spiricom/Electrobass_embedded/slider/Electrobass_slider/Electrobass_slider.cydsn/codegentemp/CapSense.h

/*******************************************************************************
* File Name: CapSense.h
* Version 2.60
*
* Description:
*  This file provides constants and parameter values for the CapSense CSD
*  component.
*
* Note:
*
********************************************************************************
* Copyright 2013-2016, Cypress Semiconductor Corporation.  All rights reserved.
* You may use this file only in accordance with the license, terms, conditions,
* disclaimers, and limitations in the end user license agreement accompanying
* the software package with which this file was provided.
*******************************************************************************/

#if !defined(CY_CAPSENSE_CSD_CapSense_H)
#define CY_CAPSENSE_CSD_CapSense_H

#include "cytypes.h"
#include "cyfitter.h"
#include "core_cm0_psoc4.h"
#include "CyLib.h"

#include "CapSense_IP.h"
#include "CapSense_SenseClk.h"
#include "CapSense_SampleClk.h"

/* Constants set by Customizer */
#define CapSense_TOTAL_SENSOR_COUNT            (11u)
#define CapSense_TOTAL_SCANSLOT_COUNT          (11u)
#define CapSense_INDEX_TABLE_SIZE              (0u)

/* Define Sensors */
#define CapSense_SENSOR_LINEARSLIDER0_E0__LS    (0u)
#define CapSense_SENSOR_LINEARSLIDER0_E1__LS    (1u)
#define CapSense_SENSOR_LINEARSLIDER0_E2__LS    (2u)
#define CapSense_SENSOR_LINEARSLIDER0_E3__LS    (3u)
#define CapSense_SENSOR_LINEARSLIDER0_E4__LS    (4u)
#define CapSense_SENSOR_LINEARSLIDER0_E5__LS    (5u)
#define CapSense_SENSOR_LINEARSLIDER0_E6__LS    (6u)
#define CapSense_SENSOR_LINEARSLIDER0_E7__LS    (7u)
#define CapSense_SENSOR_LINEARSLIDER0_E8__LS    (8u)
#define CapSense_SENSOR_BUTTON0__BTN    (9u)
#define CapSense_SENSOR_BUTTON1__BTN    (10u)

#define CapSense_TOTAL_SENSOR_MASK (((CapSense_TOTAL_SENSOR_COUNT - 1u) / 8u) + 1u)

/* Interrupt handler */
CY_ISR_PROTO(CapSense_ISR);

/* ISR Number and Priority to work with CyLib functions */
#define CapSense_ISR_NUMBER        (CapSense_ISR__INTC_NUMBER)
#define CapSense_ISR_PRIORITY      (CapSense_ISR__INTC_PRIOR_NUM)

/***************************************
*   Condition compilation parameters
***************************************/

#define CapSense_CONNECT_INACTIVE_SNS       (0u)
#define CapSense_IS_COMPLEX_SCANSLOTS       (0u)
#define CapSense_COMPLEX_SCANSLOTS_NUM      (0u)
#define CapSense_DEDICATED_SENSORS_NUM      (0u)
#define CapSense_PORT_PIN_CONFIG_TBL_ZISE   (11u)

#define CapSense_IDAC_CNT                   (2u)
#define CapSense_IDAC1_POLARITY             (0u)
#define CapSense_IDAC1_RANGE_VALUE          (0u)
#define CapSense_IDAC2_RANGE_VALUE          (0u)

#define CapSense_MULTIPLE_FREQUENCY_SET     (1u)
#define CapSense_FILTER_ENABLE              (0u)
#define CapSense_PRS_OPTIONS                (0u)

#define CapSense_WATER_PROOF                (0u)

#define CapSense_TUNING_METHOD              (0u)
#define CapSense_TUNER_API_GENERATE         (0u)

#define CapSense_CSHL_API_GENERATE          (1u)

#define CapSense_CMOD_PREGARGE_OPTION       (1u)
#define CapSense_CSH_TANK_PREGARGE_OPTION   (1u)
#define CapSense_IS_SHIELD_ENABLE           (0u)
#define CapSense_CSH_TANK_ENABLE            (0u)

#define CapSense_SHIELD_DELAY               (0u)
#define CapSense_AUTOCALIBRATION_ENABLE     (0u)

#define CapSense_IS_OVERSAMPLING_EN         (1u)

#define CapSense_CSD_4B_PWM_MODE            (0u)
#define CapSense_CSD_4B_PWM_COUNT           (0u)

/**************************************
*    Enumerated Types and Parameters
**************************************/

/* Current source definitions */
#define CapSense__IDAC_SOURCE 0
#define CapSense__IDAC_SINK 1

#define CapSense__IDAC_4X 0
#define CapSense__IDAC_8X 1

#define CapSense__PRS_NONE 0
#define CapSense__PRS_8BITS 1
#define CapSense__PRS_12BITS 2
#define CapSense__PRS_AUTO 3

/* Connection of inactive sensors definitions */
#define CapSense__GROUND 0
#define CapSense__HIZ_ANALOG 1
#define CapSense__SHIELD 2

/* Precharge options definitions */
#define CapSense__CAPPRIOBUF 0
#define CapSense__CAPPRVREF 1

/* Method of tuning */
#define CapSense__TUNING_NONE 0
#define CapSense__TUNING_MANUAL 1
#define CapSense__TUNING_AUTO 2

/* Dead band PWM modulator options */
#define CapSense__PWM_OFF 0
#define CapSense__PWM_HIGH 2
#define CapSense__PWM_LOW 3


#define CapSense_DELAY_EXTRACYCLES_NUM          (9u)
#define CapSense_GLITCH_ELIMINATION_TIMEOUT     (0u)
#define CapSense_GLITCH_ELIMINATION_CYCLES_CALC (CapSense_GLITCH_ELIMINATION_TIMEOUT * CYDEV_BCLK__SYSCLK__MHZ)

#if(CapSense_GLITCH_ELIMINATION_CYCLES_CALC >= CapSense_DELAY_EXTRACYCLES_NUM)
    #define CapSense_GLITCH_ELIMINATION_CYCLES (CapSense_GLITCH_ELIMINATION_CYCLES_CALC -\
                                                        CapSense_DELAY_EXTRACYCLES_NUM)
#else
    #define CapSense_GLITCH_ELIMINATION_CYCLES (CapSense_GLITCH_ELIMINATION_CYCLES_CALC)
#endif /* (CapSense_GLITCH_ELIMINATION_CYCLES_CALC >= CapSense_DELAY_EXTRACYCLES_NUM) */

#define CapSense_INITIAL_CLK_DIVIDER            (CYDEV_BCLK__HFCLK__KHZ / CYDEV_BCLK__SYSCLK__KHZ)


/* Structure to save registers before going to sleep */
typedef struct
{
    uint8 enableState;
} CapSense_BACKUP_STRUCT;


/***************************************
*        Function Prototypes
***************************************/
void CapSense_Init(void);
void CapSense_CsdHwBlockInit(void);
void CapSense_Enable(void);
void CapSense_Start(void);
void CapSense_Stop(void);
void CapSense_SaveConfig(void);
void CapSense_Sleep(void);
void CapSense_RestoreConfig(void);
void CapSense_Wakeup(void);
uint32 CapSense_IsBusy(void);
void CapSense_ScanSensor(uint32 sensor);
void CapSense_ScanWidget(uint32 widget);
void CapSense_ScanEnabledWidgets(void);
uint16 CapSense_ReadSensorRaw(uint32 sensor);
void CapSense_WriteSensorRaw(uint32 sensor, uint16 value);
void CapSense_ClearSensors(void);
void CapSense_SetShieldDelay(uint32 delay);
uint32 CapSense_ReadCurrentScanningSensor(void);

uint32 CapSense_GetScanResolution(uint32 widget);
uint32 CapSense_GetSenseClkDivider(uint32 sensor);
uint32 CapSense_GetModulatorClkDivider(uint32 sensor);
uint32 CapSense_GetModulationIDAC(uint32 sensor);
uint32 CapSense_GetCompensationIDAC(uint32 sensor);
uint32 CapSense_GetIDACRange(void);

#if (CapSense_TUNING_METHOD != CapSense__TUNING_NONE)
    void CapSense_SetScanResolution(uint32 widget, uint32 resolution);
    void CapSense_SetSenseClkDivider(uint32 sensor, uint32 senseClk);
    void CapSense_SetModulatorClkDivider(uint32 sensor, uint32 modulatorClk);
    void CapSense_SetModulationIDAC(uint32 sensor, uint32 modIdacValue);
    void CapSense_SetCompensationIDAC(uint32 sensor, uint32 compIdacValue);
    void CapSense_SetIDACRange(uint32 iDacRange);
#endif /* (CapSense_TUNING_METHOD != CapSense__TUNING_NONE) */


void CapSense_SetDriveModeAllPins(uint32 driveMode);
void CapSense_RestoreDriveModeAllPins(void);
void CapSense_SetUnscannedSensorState(uint32 sensor, uint32 sensorState);
void CapSense_NormalizeWidgets(uint32 widgetsNum, uint8 dataPtr[]);

/***************************************
*           API Constants
***************************************/

/* PWM Resolution */
#define CapSense_CNT_MSB_RESOLUTION_8_BITS  (0x00u)
#define CapSense_CNT_MSB_RESOLUTION_9_BITS  (0x01u)
#define CapSense_CNT_MSB_RESOLUTION_10_BITS (0x03u)
#define CapSense_CNT_MSB_RESOLUTION_11_BITS (0x07u)
#define CapSense_CNT_MSB_RESOLUTION_12_BITS (0x0Fu)
#define CapSense_CNT_MSB_RESOLUTION_13_BITS (0x1Fu)
#define CapSense_CNT_MSB_RESOLUTION_14_BITS (0x3Fu)
#define CapSense_CNT_MSB_RESOLUTION_15_BITS (0x7Fu)
#define CapSense_CNT_MSB_RESOLUTION_16_BITS (0xFFu)

#define CapSense_ONE_CYCLE                  (0x00010000Lu)

#define CapSense_WINDOW_APPEND              (0xFFFF0000Lu)
#define CapSense_RESOLUTION_6_BITS          (0x003F0000Lu)
#define CapSense_RESOLUTION_7_BITS          (0x007F0000Lu)
#define CapSense_RESOLUTION_8_BITS          (0x00FF0000Lu)
#define CapSense_RESOLUTION_9_BITS          (0x01FF0000Lu)
#define CapSense_RESOLUTION_10_BITS         (0x03FF0000Lu)
#define CapSense_RESOLUTION_11_BITS         (0x07FF0000Lu)
#define CapSense_RESOLUTION_12_BITS         (0x0FFF0000Lu)
#define CapSense_RESOLUTION_13_BITS         (0x1FFF0000Lu)
#define CapSense_RESOLUTION_14_BITS         (0x3FFF0000Lu)
#define CapSense_RESOLUTION_15_BITS         (0x7FFF0000Lu)
#define CapSense_RESOLUTION_16_BITS         (0xFFFF0000Lu)

#define CapSense_RESOLUTION_OFFSET          (16u)
#define CapSense_MSB_RESOLUTION_OFFSET      (22u)
#define CapSense_RESOLUTIONS_TBL_SIZE       (3u)

/* Software Status Register Bit Masks */
#define CapSense_SW_STS_BUSY                (0x01u)
/* Software Control Register Bit Masks */
#define CapSense_SW_CTRL_SINGLE_SCAN        (0x80u)

/* Software Control Register Bit Masks for scanning one widget */
#define CapSense_SW_CTRL_WIDGET_SCAN        (0x40u)

/* Flag for complex scan slot */
#define CapSense_COMPLEX_SS_FLAG            (0x80u)

/* Flag for scanning is complete */
#define CapSense_NOT_SENSOR                 (0xFFFFFFFFLu)

/* Number of bits for each pin in PC register. */
#define CapSense_PC_PIN_CFG_SIZE            (0x03u)

/* Number of bits for each pin in HSIOM register. */
#define CapSense_HSIOM_PIN_CFG_SIZE         (0x04u)

#define CapSense_CFG_REG_TBL_SIZE           (5u)

/***************************************
*             Registers
***************************************/

#define CapSense_CSD_ID_REG             (*(reg32 *)  CapSense_CSD_FFB__CSD_ID)
#define CapSense_CSD_ID_PTR             ( (reg32 *)  CapSense_CSD_FFB__CSD_ID)

#define CapSense_CSD_CFG_REG            (*(reg32 *)  CapSense_CSD_FFB__CSD_CONFIG)
#define CapSense_CSD_CFG_PTR            ( (reg32 *)  CapSense_CSD_FFB__CSD_CONFIG)

#define CapSense_CSD_IDAC_REG           (*(reg32 *)  CapSense_IDAC1_cy_psoc4_idac__CSD_IDAC)
#define CapSense_CSD_IDAC_PTR           ( (reg32 *)  CapSense_IDAC1_cy_psoc4_idac__CSD_IDAC)

#define CapSense_CSD_CNT_REG            (*(reg32 *) CapSense_CSD_FFB__CSD_COUNTER)
#define CapSense_CSD_CNT_PTR            ( (reg32 *) CapSense_CSD_FFB__CSD_COUNTER)

#define CapSense_CSD_STAT_REG           (*(reg32 *) CapSense_CSD_FFB__CSD_STATUS)
#define CapSense_CSD_STAT_PTR           ( (reg32 *) CapSense_CSD_FFB__CSD_STATUS)

#define CapSense_CSD_INTR_REG           (*(reg32 *) CapSense_CSD_FFB__CSD_INTR)
#define CapSense_CSD_INTR_PTR           ( (reg32 *) CapSense_CSD_FFB__CSD_INTR)

#define CapSense_CSD_INTR_SET_REG       (*(reg32 *) CapSense_CSD_FFB__CSD_INTR_SET)
#define CapSense_CSD_INTR_SET_PTR       ( (reg32 *) CapSense_CSD_FFB__CSD_INTR_SET)

#define CapSense_CSD_4B_PWM_REG         (*(reg32 *) CapSense_CSD_FFB__CSD_PWM)
#define CapSense_CSD_4B_PWM_PTR         ( (reg32 *) CapSense_CSD_FFB__CSD_PWM)

#define CapSense_CSD_TRIM1_REG          (*(reg32 *) CapSense_IDAC1_cy_psoc4_idac__CSD_TRIM1)
#define CapSense_CSD_TRIM1_PTR          ( (reg32 *) CapSense_IDAC1_cy_psoc4_idac__CSD_TRIM1)

#define CapSense_CSD_TRIM2_REG          (*(reg32 *) CapSense_IDAC1_cy_psoc4_idac__CSD_TRIM2)
#define CapSense_CSD_TRIM2_PTR          ( (reg32 *) CapSense_IDAC1_cy_psoc4_idac__CSD_TRIM2)

#if (2u == CapSense_M0S8CSD_BLOCK_CNT)
    #if (CapSense_CSD_FFB__CSD_NUMBER != 1u)
        #define CapSense_SFLASH_CSD_TRIM1_REG   (*(reg8 *) CYREG_SFLASH_CSD_TRIM1_CSD)
        #define CapSense_SFLASH_CSD_TRIM1_PTR   ( (reg8 *) CYREG_SFLASH_CSD_TRIM1_CSD)

        #define CapSense_SFLASH_CSD_TRIM2_REG   (*(reg8 *) CYREG_SFLASH_CSD_TRIM2_CSD)
        #define CapSense_SFLASH_CSD_TRIM2_PTR   ( (reg8 *) CYREG_SFLASH_CSD_TRIM2_CSD)
    #else
        #define CapSense_SFLASH_CSD_TRIM1_REG   (*(reg8 *) CYREG_SFLASH_CSD1_TRIM1_CSD)
        #define CapSense_SFLASH_CSD_TRIM1_PTR   ( (reg8 *) CYREG_SFLASH_CSD1_TRIM1_CSD)

        #define CapSense_SFLASH_CSD_TRIM2_REG   (*(reg8 *) CYREG_SFLASH_CSD1_TRIM2_CSD)
        #define CapSense_SFLASH_CSD_TRIM2_PTR   ( (reg8 *) CYREG_SFLASH_CSD1_TRIM2_CSD)
    #endif /* (CapSense_CSD_FFB__CSD_NUMBER != 1u) */
#else
    #define CapSense_SFLASH_CSD_TRIM1_REG   (*(reg8 *) CYREG_SFLASH_CSD_TRIM1_CSD)
    #define CapSense_SFLASH_CSD_TRIM1_PTR   ( (reg8 *) CYREG_SFLASH_CSD_TRIM1_CSD)

    #define CapSense_SFLASH_CSD_TRIM2_REG   (*(reg8 *) CYREG_SFLASH_CSD_TRIM2_CSD)
    #define CapSense_SFLASH_CSD_TRIM2_PTR   ( (reg8 *) CYREG_SFLASH_CSD_TRIM2_CSD)
#endif /* (2u == CapSense_M0S8CSD_BLOCK_CNT) */

/* Port function select */
#define CapSense_PORT_SEL0_REG          (*(reg32 *) CYREG_HSIOM_PORT_SEL0 )
#define CapSense_PORT_SEL0_PTR          (*(reg32 *) CYREG_HSIOM_PORT_SEL0 )

#define CapSense_PORT_SEL1_REG          (*(reg32 *) CYREG_HSIOM_PORT_SEL1 )
#define CapSense_PORT_SEL1_PTR          (*(reg32 *) CYREG_HSIOM_PORT_SEL1 )

#define CapSense_PORT_SEL2_REG          (*(reg32 *) CYREG_HSIOM_PORT_SEL2 )
#define CapSense_PORT_SEL2_PTR          (*(reg32 *) CYREG_HSIOM_PORT_SEL2 )

#define CapSense_PORT_SEL3_REG          (*(reg32 *) CYREG_HSIOM_PORT_SEL3 )
#define CapSense_PORT_SEL3_PTR          (*(reg32 *) CYREG_HSIOM_PORT_SEL3 )

#define CapSense_PORT_SEL4_REG          (*(reg32 *) CYREG_HSIOM_PORT_SEL4 )
#define CapSense_PORT_SEL4_PTR          (*(reg32 *) CYREG_HSIOM_PORT_SEL4 )


#define CapSense_PORT0_PC_REG          (*(reg32 *) CYREG_PRT0_PC )
#define CapSense_PORT0_PC_PTR          (*(reg32 *) CYREG_PRT0_PC )

#define CapSense_PORT1_PC_REG          (*(reg32 *) CYREG_PRT1_PC )
#define CapSense_PORT1_PC_PTR          (*(reg32 *) CYREG_PRT1_PC )

#define CapSense_PORT2_PC_REG          (*(reg32 *) CYREG_PRT2_PC )
#define CapSense_PORT2_PC_PTR          (*(reg32 *) CYREG_PRT2_PC )

#define CapSense_PORT3_PC_REG          (*(reg32 *) CYREG_PRT3_PC )
#define CapSense_PORT3_PC_PTR          (*(reg32 *) CYREG_PRT3_PC )

#define CapSense_PORT4_PC_REG          (*(reg32 *) CYREG_PRT4_PC )
#define CapSense_PORT4_PC_PTR          (*(reg32 *) CYREG_PRT4_PC )


#define CapSense_PORT0_DR_REG          (*(reg32 *) CYREG_PRT0_DR )
#define CapSense_PORT0_DR_PTR          (*(reg32 *) CYREG_PRT0_DR )

#define CapSense_PORT1_DR_REG          (*(reg32 *) CYREG_PRT1_DR )
#define CapSense_PORT1_DR_PTR          (*(reg32 *) CYREG_PRT1_DR )

#define CapSense_PORT2_DR_REG          (*(reg32 *) CYREG_PRT2_DR )
#define CapSense_PORT2_DR_PTR          (*(reg32 *) CYREG_PRT2_DR )

#define CapSense_PORT3_DR_REG          (*(reg32 *) CYREG_PRT3_DR )
#define CapSense_PORT3_DR_PTR          (*(reg32 *) CYREG_PRT3_DR )

#define CapSense_PORT4_DR_REG          (*(reg32 *) CYREG_PRT4_DR )
#define CapSense_PORT4_DR_PTR          (*(reg32 *) CYREG_PRT4_DR )



#define CapSense_CMOD_CONNECTION_REG        (*(reg32 *) CapSense_Cmod__0__HSIOM)
#define CapSense_CMOD_PORT_PC_REG           (*(reg32 *) CapSense_Cmod__0__PC)
#define CapSense_CMOD_PORT_DR_REG           (*(reg32 *) CapSense_Cmod__0__DR)

#define CapSense_CTANK_CONNECTION_REG       (*(reg32 *) CapSense_Csh_tank__0__HSIOM)
#define CapSense_CTANK_PORT_PC_REG          (*(reg32 *) CapSense_Csh_tank__0__PC)
#define CapSense_CTANK_PORT_DR_REG          (*(reg32 *) CapSense_Csh_tank__0__DR)

/***************************************
*       Register Constants
***************************************/

/* Port configuration defines */
#define CapSense_CSD_HSIOM_MASK                 (0x0000000FLu)

#define CapSense_CSD_SENSE_PORT_MODE            (0x00000004Lu)
#define CapSense_CSD_SHIELD_PORT_MODE           (0x00000005Lu)

#define CapSense_AMUXA_CONNECTION_MODE          (0x00000006Lu)
#define CapSense_AMUXB_CONNECTION_MODE          (0x00000007Lu)

#define CapSense_CSD_PIN_MODE_MASK              (0x00000007Lu)
#define CapSense_CSD_PIN_DRIVE_MASK             (0x00000001Lu)

#define CapSense_CSD_PIN_DM_STRONG              (0x00000006Lu)
#define CapSense_CSD_PIN_DM_HIGH_Z              (0x00000000Lu)

#define CapSense_CSD_CMOD_CONNECTION_MASK   (uint32)(CapSense_Cmod__0__HSIOM_MASK)
#define CapSense_CSD_CMOD_TO_AMUXBUS_A      (uint32)(CapSense_AMUXA_CONNECTION_MODE << CapSense_Cmod__0__HSIOM_SHIFT)
#define CapSense_CSD_CMOD_TO_AMUXBUS_B      (uint32)(CapSense_AMUXB_CONNECTION_MODE << CapSense_Cmod__0__HSIOM_SHIFT)

#if(0u != CapSense_CSH_TANK_ENABLE)
    #define CapSense_CSD_CTANK_CONNECTION_MASK  (uint32)(CapSense_Csh_tank__0__HSIOM_MASK)
    #define CapSense_CSD_CTANK_TO_AMUXBUS_A     (uint32)(CapSense_AMUXA_CONNECTION_MODE << CapSense_Csh_tank__0__HSIOM_SHIFT)
    #define CapSense_CSD_CTANK_TO_AMUXBUS_B     (uint32)(CapSense_AMUXB_CONNECTION_MODE << CapSense_Csh_tank__0__HSIOM_SHIFT)
#endif /* (0u != CapSense_CSH_TANK_ENABLE) */

#define  CapSense_CSD_CMOD_PC_MASK          (uint32)(CapSense_CSD_PIN_MODE_MASK <<\
                                                            ((uint32)CapSense_Cmod__0__SHIFT * CapSense_PC_PIN_CFG_SIZE))
#define  CapSense_CMOD_PC_STRONG_MODE       (uint32)(CapSense_CSD_PIN_DM_STRONG <<\
                                                            ((uint32)CapSense_Cmod__0__SHIFT * CapSense_PC_PIN_CFG_SIZE))
#define  CapSense_CMOD_PC_HIGH_Z_MODE       (uint32)(CapSense_CSD_PIN_DM_HIGH_Z <<\
                                                            ((uint32)CapSense_Cmod__0__SHIFT * CapSense_PC_PIN_CFG_SIZE))

#if(0u != CapSense_CSH_TANK_ENABLE)
    #define  CapSense_CSD_CTANK_PC_MASK         (uint32)(CapSense_CSD_PIN_MODE_MASK <<\
                                                                ((uint32)CapSense_Csh_tank__0__SHIFT * CapSense_PC_PIN_CFG_SIZE))
    #define  CapSense_CTANK_PC_STRONG_MODE      (uint32)(CapSense_CSD_PIN_DM_STRONG <<\
                                                                ((uint32)CapSense_Csh_tank__0__SHIFT * CapSense_PC_PIN_CFG_SIZE))
    #define  CapSense_CTANK_PC_HIGH_Z_MODE      (uint32)(CapSense_CSD_PIN_DM_HIGH_Z <<\
                                                                ((uint32)CapSense_Csh_tank__0__SHIFT * CapSense_PC_PIN_CFG_SIZE))
#endif /* (0u != CapSense_CSH_TANK_ENABLE) */

#define  CapSense_CMOD_DR_VSSIO             (uint32)(CapSense_Cmod__0__MASK)
#define  CapSense_CMOD_DR_VDDIO             (0x00000000Lu)
#define  CapSense_CMOD_DR_MASK              (uint32)(CapSense_Cmod__0__MASK)

#if(0u != CapSense_CSH_TANK_ENABLE)
    #define  CapSense_CTANK_DR_VSSIO            (uint32)(CapSense_Csh_tank__0__MASK)
    #define  CapSense_CTANK_DR_VDDIO            (0x00000000Lu)
    #define  CapSense_CTANK_DR_MASK             (uint32)(CapSense_Csh_tank__0__MASK)
#endif /* (0u != CapSense_CSH_TANK_ENABLE) */

#define  CapSense_CMOD_PIN_NUMBER               (CapSense_Cmod__0__SHIFT)
#define  CapSense_CMOD_PRT_NUMBER               (CapSense_Cmod__0__PORT)

#if(0u != CapSense_CSH_TANK_ENABLE)
    #define  CapSense_CTANK_PIN_NUMBER          (CapSense_Csh_tank__0__SHIFT)
    #define  CapSense_CTANK_PRT_NUMBER          (CapSense_Csh_tank__0__PORT)
#endif /* (0u != CapSense_CSH_TANK_ENABLE) */

/* ID register fields position */
#define CapSense_CSD_ID_ID__POS                 (0x00u)
#define CapSense_CSD_ID_REV__POS                (0x10u)

#define CapSense_CSD_ID_ID                      (0xFFLu << CapSense_CSD_ID_ID__POS)
#define CapSense_CSD_ID_REV                     (0xFFLu << CapSense_CSD_ID_REV__POS)

/* CSD_CONFIG register fields position */
#define CapSense_CSD_CFG_DSI_SAMPLE_EN_POS      (0x00u)
#define CapSense_CSD_CFG_SAMPLE_SYNC_POS        (0x01u)
#define CapSense_CSD_CFG_FILTER_EN_POS          (0x03u)
#define CapSense_CSD_CFG_PRS_CLEAR_POS          (0x05u)
#define CapSense_CSD_CFG_PRS_SELECT_POS         (0x06u)
#define CapSense_CSD_CFG_PRS_12_8_POS           (0x07u)
#define CapSense_CSD_CFG_DSI_SENSE_EN_POS       (0x08u)
#define CapSense_CSD_CFG_SHIELD_DELAY_POS       (0x09u)
#define CapSense_CSD_CFG_SENSE_COMP_BW_POS      (0x0Bu)
#define CapSense_CSD_CFG_SENSE_EN_POS           (0x0Cu)
#define CapSense_CSD_CFG_REFBUF_EN_POS          (0x0Du)
#define CapSense_CSD_CFG_CHARGE_IO_POS          (0x0Eu)
#define CapSense_CSD_CFG_COMP_PIN_POS           (0x0Fu)
#define CapSense_CSD_CFG_POLARITY_POS           (0x10u)
#define CapSense_CSD_CFG_MUTUAL_CAP_POS         (0x12u)
#define CapSense_CSD_CFG_SENSE_COMP_EN_POS      (0x13u)
#define CapSense_CSD_CFG_REFBUF_OUTSEL_POS      (0x15u)
#define CapSense_CSD_CFG_SENSE_INSEL_POS        (0x16u)
#define CapSense_CSD_REFBUF_DRV_POS             (0x17u)
#define CapSense_CSD_CFG_DDFTSEL_POS            (0x1Au)
#define CapSense_CSD_CFG_ADFTEN_POS             (0x1Du)
#define CapSense_CSD_CFG_DDFTCOMP_POS           (0x1Eu)
#define CapSense_CSD_CFG_ENABLE_POS             (0x1Fu)

/* CSD_STATUS register fields position */
#define CapSense_CSD_STAT_CSD_CHARGE_POS        (0x00u)
#define CapSense_CSD_STAT_CSD_SENSE_POS         (0x01u)
#define CapSense_CSD_STAT_COMP_OUT_POS          (0x02u)
#define CapSense_CSD_STAT_SAMPLE_POS            (0x03u)

/* CSD_IDAC control register fields position */
#define CapSense_CSD_IDAC1_MODE_MASK_POS        (0x08u)
#define CapSense_CSD_IDAC1_MODE_FIXED_POS       (0x08u)
#define CapSense_CSD_IDAC1_MODE_VARIABLE_POS    (0x08u)
#define CapSense_CSD_IDAC1_MODE_DSI_POS         (0x08u)
#define CapSense_CSD_IDAC1_RANGE_8X_POS         (0x0Au)
#define CapSense_CSD_IDAC1_DATA_MASK_POS        (0x00u)

#define CapSense_CSD_IDAC2_MODE_MASK_POS        (0x18u)
#define CapSense_CSD_IDAC2_MODE_FIXED_POS       (0x18u)
#define CapSense_CSD_IDAC2_MODE_VARIABLE_POS    (0x18u)
#define CapSense_CSD_IDAC2_MODE_DSI_POS         (0x18u)
#define CapSense_CSD_IDAC2_RANGE_8X_POS         (0x1Au)
#define CapSense_CSD_IDAC2_DATA_MASK_POS        (0x10u)

/* CSD_COUNTER register fields position */
#define CapSense_CSD_CNT_COUNTER_POS            (0x00u)
#define CapSense_CSD_CNT_PERIOD_POS             (0x10u)

/* CSD_CONFIRG register definitions */
#define CapSense_CSD_CFG_DSI_SAMPLE_EN          (0x01Lu << CapSense_CSD_CFG_DSI_SAMPLE_EN_POS)
#define CapSense_CSD_CFG_SAMPLE_SYNC            (0x01Lu << CapSense_CSD_CFG_SAMPLE_SYNC_POS)
#define CapSense_CSD_CFG_FILTER_EN              (0x01Lu << CapSense_CSD_CFG_FILTER_EN_POS)
#define CapSense_CSD_CFG_PRS_CLEAR              (0x01Lu << CapSense_CSD_CFG_PRS_CLEAR_POS)
#define CapSense_CSD_CFG_PRS_SELECT             (0x01Lu << CapSense_CSD_CFG_PRS_SELECT_POS)
#define CapSense_CSD_CFG_PRS_12_8               (0x01Lu << CapSense_CSD_CFG_PRS_12_8_POS)
#define CapSense_CSD_CFG_DSI_SENSE_EN           (0x01Lu << CapSense_CSD_CFG_DSI_SENSE_EN_POS)
#define CapSense_CSD_CFG_SHIELD_DELAY_MASK      (0x03Lu << CapSense_CSD_CFG_SHIELD_DELAY_POS)
#define CapSense_CSD_CFG_SENSE_COMP_BW          (0x01Lu << CapSense_CSD_CFG_SENSE_COMP_BW_POS)
#define CapSense_CSD_CFG_SENSE_EN               (0x01Lu << CapSense_CSD_CFG_SENSE_EN_POS)
#define CapSense_CSD_CFG_REFBUF_EN              (0x01Lu << CapSense_CSD_CFG_REFBUF_EN_POS)
#define CapSense_CSD_CFG_CHARGE_IO              (0x01Lu << CapSense_CSD_CFG_CHARGE_IO_POS)
#define CapSense_CSD_CFG_COMP_PIN_CH2           (0x01Lu << CapSense_CSD_CFG_COMP_PIN_POS)
#define CapSense_CSD_CFG_POLARITY_VDDIO         (0x01Lu << CapSense_CSD_CFG_POLARITY_POS)
#define CapSense_CSD_CFG_MUTUAL_CAP             (0x01Lu << CapSense_CSD_CFG_MUTUAL_CAP_POS)
#define CapSense_CSD_CFG_SENSE_COMP_EN          (0x01Lu << CapSense_CSD_CFG_SENSE_COMP_EN_POS)
#define CapSense_CSD_CFG_REFBUF_OUTSEL          (0x01Lu << CapSense_CSD_CFG_REFBUF_OUTSEL_POS)
#define CapSense_CSD_CFG_SENSE_INSEL            (0x01Lu << CapSense_CSD_CFG_SENSE_INSEL_POS)
#define CapSense_CSD_REFBUF_DRV_MASK            (0x03Lu << CapSense_CSD_REFBUF_DRV_POS)
#define CapSense_CSD_REFBUF_DRV_LOW             (0x01Lu << CapSense_CSD_REFBUF_DRV_POS)
#define CapSense_CSD_REFBUF_DRV_MEDIUM          (0x02Lu << CapSense_CSD_REFBUF_DRV_POS)
#define CapSense_CSD_REFBUF_DRV_HIGH            (0x03Lu << CapSense_CSD_REFBUF_DRV_POS)
#define CapSense_CSD_CFG_DDFTSEL_MASK           (0x07Lu << CapSense_CSD_CFG_DDFTSEL_POS)
#define CapSense_CSD_CFG_ADFTEN                 (0x01Lu << CapSense_CSD_CFG_ADFTEN_POS)
#define CapSense_CSD_CFG_DDFTCOMP_MASK          (0x03Lu << CapSense_CSD_CFG_DDFTCOMP_POS)
#define CapSense_CSD_CFG_DDFTCOMP_REFCOMP       (0x01Lu << CapSense_CSD_CFG_DDFTCOMP_POS)
#define CapSense_CSD_CFG_DDFTCOMP_SENSECOMP     (0x02Lu << CapSense_CSD_CFG_DDFTCOMP_POS)
#define CapSense_CSD_CFG_ENABLE                 (0x01Lu << CapSense_CSD_CFG_ENABLE_POS)

/* CSD_STATUS register definitions */
#define CapSense_CSD_STAT_CSD_CHARGE            (0x01Lu << CapSense_CSD_STAT_CSD_CHARGE_POS)
#define CapSense_CSD_STAT_CSD_SENSE             (0x01Lu << CapSense_CSD_STAT_CSD_SENSE_POS)
#define CapSense_CSD_STAT_COMP_OUT              (0x01Lu << CapSense_CSD_STAT_COMP_OUT_POS)
#define CapSense_CSD_STAT_SAMPLE                (0x01Lu << CapSense_CSD_STAT_SAMPLE_POS)

/* CSD_IDAC control register definitions */
#define CapSense_CSD_IDAC1_MODE_MASK            (0x03Lu << CapSense_CSD_IDAC1_MODE_MASK_POS)
#define CapSense_CSD_IDAC1_MODE_FIXED           (0x01Lu << CapSense_CSD_IDAC1_MODE_FIXED_POS)
#define CapSense_CSD_IDAC1_MODE_VARIABLE        (0x02Lu << CapSense_CSD_IDAC1_MODE_VARIABLE_POS)
#define CapSense_CSD_IDAC1_MODE_DSI             (0x03Lu << CapSense_CSD_IDAC1_MODE_DSI_POS)
#define CapSense_CSD_IDAC1_RANGE_8X             (0x01Lu << CapSense_CSD_IDAC1_RANGE_8X_POS)
#define CapSense_CSD_IDAC1_DATA_MASK            (0xFFLu << CapSense_CSD_IDAC1_DATA_MASK_POS)

#define CapSense_CSD_IDAC2_MODE_MASK            (0x03Lu << CapSense_CSD_IDAC2_MODE_MASK_POS)
#define CapSense_CSD_IDAC2_MODE_FIXED           (0x01Lu << CapSense_CSD_IDAC2_MODE_FIXED_POS)
#define CapSense_CSD_IDAC2_MODE_VARIABLE        (0x02Lu << CapSense_CSD_IDAC2_MODE_VARIABLE_POS)
#define CapSense_CSD_IDAC2_MODE_DSI             (0x03Lu << CapSense_CSD_IDAC2_MODE_DSI_POS)
#define CapSense_CSD_IDAC2_RANGE_8X             (0x01Lu << CapSense_CSD_IDAC2_RANGE_8X_POS)
#define CapSense_CSD_IDAC2_DATA_MASK            (0x7FLu << CapSense_CSD_IDAC2_DATA_MASK_POS)

#define CapSense_CSD_IDAC2_DATA_OFFSET          (16u)

#define CapSense_CSD_IDAC1_TRIM_MASK            (0xFFFFFFF0u)
#define CapSense_CSD_IDAC2_TRIM_MASK            (0xFFFFFF0Fu)

#define CapSense_CSFLASH_TRIM_IDAC1_MASK        (0x0Fu)
#define CapSense_CSFLASH_TRIM_IDAC2_MASK        (0xF0)

#define CapSense_CSD_4B_PWM_MODE_OFFSET         (4u)
#define CapSense_CSD_4B_PWM_MODE_DEFAULT        (CapSense_CSD_4B_PWM_MODE << CapSense_CSD_4B_PWM_MODE_OFFSET)

#define CapSense_CSD_4B_PWM_COUNT_MASK          (0x0000000Fu)
#define CapSense_CSD_4B_PWM_MODE_MASK           (0x00000030u)

#define CapSense_CSD_IDAC_PRECHARGE_CONFIG      (CapSense_CSD_IDAC1_MODE_FIXED |\
                                                        CapSense_PRECHARGE_IDAC1_VAL)

/* CSD_COUNTER register definitions */
#define CapSense_CSD_CNT_COUNTER                (0xFFLu << CapSense_CSD_CNT_COUNTER_POS )
#define CapSense_CSD_CNT_PERIOD                 (0xFFLu << CapSense_CSD_CNT_PERIOD_POS)

#define CapSense_CSD_PRS_8_BIT                  (0x00000000u)
#define CapSense_CSD_PRS_12_BIT                 (CapSense_CSD_CFG_PRS_12_8)
#define CapSense_PRS_MODE_MASK                  (CapSense_CSD_CFG_PRS_12_8)

/***************************************
*    Initial Parameter Constants
***************************************/

#if (0u != CapSense_FILTER_ENABLE)
    #define CapSense_DEFAULT_FILTER_STATE       (CapSense_CSD_CFG_FILTER_EN)

#else
    #define CapSense_DEFAULT_FILTER_STATE       (0u)

#endif /* (CapSense_PRS_OPTIONS == CapSense_PRS_8BITS) */

#define CapSense_DEFAULT_CSD_4B_PWM_CONFIG      (CapSense_CSD_4B_PWM_MODE_DEFAULT | CapSense_CSD_4B_PWM_COUNT)

/* Set PRS */
#if (CapSense_PRS_OPTIONS == CapSense__PRS_8BITS)
    #define CapSense_DEFAULT_MODULATION_MODE    CapSense_CSD_CFG_PRS_SELECT

#elif (CapSense_PRS_OPTIONS == CapSense__PRS_12BITS)
    #define CapSense_DEFAULT_MODULATION_MODE    (CapSense_CSD_CFG_PRS_12_8 |\
                                                        CapSense_CSD_CFG_PRS_SELECT)
#else
    #define CapSense_DEFAULT_MODULATION_MODE    (0u)
#endif /* (CapSense_PRS_OPTIONS == CapSense_PRS_8BITS) */

/* Set IDAC ranges */
#if (CapSense_IDAC1_RANGE_VALUE == CapSense__IDAC_8X)
    #define CapSense_DEFAULT_IDAC1_RANGE        CapSense_CSD_IDAC1_RANGE_8X
    #define CapSense_DEFAULT_IDAC2_RANGE        CapSense_CSD_IDAC2_RANGE_8X
#else
    #define CapSense_DEFAULT_IDAC1_RANGE        (0u)
    #define CapSense_DEFAULT_IDAC2_RANGE        (0u)
#endif /* (CapSense_IDAC1_RANGE_VALUE == CapSense_IDAC_RANGE_8X) */

/* Set IDAC polarity */
#if(CapSense_IDAC1_POLARITY == CapSense__IDAC_SINK)

    #define CapSense_DEFAULT_IDAC_POLARITY      CapSense_CSD_CFG_POLARITY_VDDIO
    #define CapSense_CMOD_DR_CONFIG             CapSense_CMOD_DR_VDDIO
    #define CapSense_CTANK_DR_CONFIG            CapSense_CTANK_DR_VDDIO
#else

    #define CapSense_DEFAULT_IDAC_POLARITY      (0u)
    #define CapSense_CMOD_DR_CONFIG             CapSense_CMOD_DR_VSSIO
    #define CapSense_CTANK_DR_CONFIG            CapSense_CTANK_DR_VSSIO
#endif /* (CapSense_IDAC_OPTIONS == CapSense_IDAC_SINK) */

#define CapSense_SNS_GROUND_CONNECT             (6u)
#define CapSense_SNS_HIZANALOG_CONNECT          (0u)

/* Inactive sensors connection configuration */
#if (CapSense_CONNECT_INACTIVE_SNS == CapSense__GROUND)
    #define CapSense_CSD_INACTIVE_CONNECT       (CapSense_SNS_GROUND_CONNECT)
#else
    #define CapSense_CSD_INACTIVE_CONNECT       (CapSense_SNS_HIZANALOG_CONNECT)
#endif /* CapSense_CONNECT_INACTIVE_SNS == CapSense__GROUND */

#if(CapSense_IS_SHIELD_ENABLE)
    #define CapSense_SHIELD_PORT_NUMBER CapSense_Shield__PORT
    #define CapSense_SHIELD_PIN_NUMBER  CapSense_Shield__SHIFT
#endif /* (CapSense_IS_SHIELD_ENABLE) */

/* Defining default CSD configuration according to settings in customizer. */
#define CapSense_DEFAULT_CSD_CONFIG             (CapSense_DEFAULT_FILTER_STATE |\
                                                         CapSense_DEFAULT_MODULATION_MODE |\
                                                         CapSense_CSD_CFG_SENSE_COMP_BW |\
                                                         CapSense_DEFAULT_IDAC_POLARITY |\
                                                         CapSense_CSD_CFG_REFBUF_OUTSEL |\
                                                         CapSense_CSD_REFBUF_DRV_HIGH)

#define CapSense_CSD_CONFIG_MASK                (CapSense_CSD_CFG_FILTER_EN |\
                                                         CapSense_CSD_CFG_PRS_SELECT |\
                                                         CapSense_CSD_CFG_PRS_12_8 |\
                                                         CapSense_CSD_CFG_SENSE_COMP_BW |\
                                                         CapSense_CSD_CFG_REFBUF_EN |\
                                                         CapSense_CSD_CFG_REFBUF_OUTSEL |\
                                                         CapSense_CSD_CFG_POLARITY_VDDIO |\
                                                         CapSense_CSD_CFG_REFBUF_OUTSEL  |\
                                                         CapSense_CSD_REFBUF_DRV_MASK)


/* Defining the default IDACs configuration according to settings in customizer. */
#if (CapSense_IDAC_CNT == 1u)
    #define CapSense_DEFAULT_CSD_IDAC_CONFIG    (CapSense_CSD_IDAC1_MODE_VARIABLE |\
                                                             CapSense_DEFAULT_IDAC1_RANGE)
#else
    #define CapSense_DEFAULT_CSD_IDAC_CONFIG    (CapSense_CSD_IDAC1_MODE_VARIABLE |\
                                                             CapSense_CSD_IDAC2_MODE_FIXED |\
                                                             CapSense_DEFAULT_IDAC1_RANGE |\
                                                             CapSense_DEFAULT_IDAC2_RANGE)
#endif /* (CapSense_IDAC_CNT == 1u) */

/* Defining mask intended for clearing bits related to pre-charging options. */
#define CapSense_PRECHARGE_CONFIG_MASK          (CapSense_CSD_CFG_REFBUF_EN |\
                                                         CapSense_CSD_CFG_CHARGE_IO |\
                                                         CapSense_CSD_CFG_COMP_PIN_CH2  |\
                                                         CapSense_CSD_CFG_REFBUF_OUTSEL)

/* Cmod the precharge mode configuration */
#if(CapSense_CMOD_PREGARGE_OPTION == CapSense__CAPPRVREF)

    #define CapSense_CMOD_PRECHARGE_CONFIG      (CapSense_CSD_CFG_REFBUF_EN |\
                                                         CapSense_CSD_CFG_COMP_PIN_CH2)

#else

    #define CapSense_CMOD_PRECHARGE_CONFIG      (CapSense_CSD_CFG_REFBUF_OUTSEL |\
                                                         CapSense_CSD_CFG_REFBUF_EN |\
                                                         CapSense_CSD_CFG_CHARGE_IO)

#endif /* (CapSense_CMOD_PREGARGE_OPTION == CapSense__CAPPRVREF) */

/* Ctank the precharge mode configuration */
#if(CapSense_CSH_TANK_PREGARGE_OPTION == CapSense__CAPPRVREF)

    #if(0u != CapSense_IS_SHIELD_ENABLE)
        #define  CapSense_CTANK_PRECHARGE_CONFIG    (CapSense_CSD_CFG_REFBUF_EN |\
                                                             CapSense_CSD_CFG_PRS_CLEAR |\
                                                             CapSense_CSD_CFG_REFBUF_OUTSEL)
    #else
        #define  CapSense_CTANK_PRECHARGE_CONFIG    (CapSense_CSD_CFG_REFBUF_OUTSEL |\
                                                             CapSense_CSD_CFG_PRS_CLEAR)
    #endif /* (0u != CapSense_IS_SHIELD_ENABLE) */

#else

    #define  CapSense_CTANK_PRECHARGE_CONFIG    (CapSense_CSD_CFG_REFBUF_OUTSEL |\
                                                         CapSense_CSD_CFG_REFBUF_EN |\
                                                         CapSense_CSD_CFG_CHARGE_IO |\
                                                         CapSense_CSD_CFG_PRS_CLEAR |\
                                                         CapSense_CSD_CFG_COMP_PIN_CH2)
#endif /* (CapSense_CSH_TANK_PREGARGE_OPTION == CapSense__CAPPRIOBUF) */

#define CapSense_MAX_UINT_8                     (0xFFu)
#define CapSense_MAX_UINT_16                    (0xFFFFu)
#define CapSense_MAX_UINT_32                    (0xFFFFFFFFLu)

/***************************************
*     Vars with External Linkage
***************************************/
/* SmartSense functions */
#if (CapSense_TUNING_METHOD == CapSense__TUNING_AUTO)
    extern uint8 CapSense_lowLevelTuningDone;
    extern uint8 CapSense_scanSpeedTbl[((CapSense_TOTAL_SENSOR_COUNT - 1u) / 8u) + 1u];
    extern void CapSense_AutoTune(void);
#endif /* (CapSense_TUNING_METHOD == CapSense__TUNING_AUTO) */

#if(CapSense_PRS_OPTIONS != CapSense__PRS_NONE)
    extern uint8 CapSense_prescalersTuningDone;
#endif /* (CapSense_PRS_OPTIONS == CapSense__PRS_NONE) */

/* Global software variables */
extern volatile uint8 CapSense_csdStatusVar;
extern volatile uint8 CapSense_sensorIndex;
extern uint16 CapSense_sensorRaw[CapSense_TOTAL_SENSOR_COUNT];
extern uint8 CapSense_unscannedSnsDriveMode[CapSense_PORT_PIN_CONFIG_TBL_ZISE];
extern uint8 CapSense_sensorEnableMaskBackup[CapSense_TOTAL_SENSOR_MASK];
extern uint8 CapSense_sensorEnableMask[CapSense_TOTAL_SENSOR_MASK];

#if ((CapSense_TUNING_METHOD != CapSense__TUNING_NONE) || (0u != CapSense_AUTOCALIBRATION_ENABLE))
    extern uint8 CapSense_modulationIDAC[CapSense_TOTAL_SENSOR_COUNT];
    extern uint8 CapSense_compensationIDAC[CapSense_TOTAL_SENSOR_COUNT];
#else
    extern const uint8 CapSense_modulationIDAC[CapSense_TOTAL_SENSOR_COUNT];
    extern const uint8 CapSense_compensationIDAC[CapSense_TOTAL_SENSOR_COUNT];
#endif /* ((CapSense_TUNING_METHOD != CapSense__TUNING_NONE) || (0u != CapSense_AUTOCALIBRATION_ENABLE)) */

#if (CapSense_TUNING_METHOD != CapSense__TUNING_NONE)
    extern uint32 CapSense_widgetResolution[CapSense_RESOLUTIONS_TBL_SIZE];
    #if (0u != CapSense_MULTIPLE_FREQUENCY_SET)
        extern uint8 CapSense_senseClkDividerVal[CapSense_TOTAL_SCANSLOT_COUNT];
        extern uint8 CapSense_sampleClkDividerVal[CapSense_TOTAL_SCANSLOT_COUNT];
    #else
        extern uint8 CapSense_senseClkDividerVal;
        extern uint8 CapSense_sampleClkDividerVal;
    #endif /* (0u != CapSense_MULTIPLE_FREQUENCY_SET) */
#else
    extern const uint32 CapSense_widgetResolution[CapSense_RESOLUTIONS_TBL_SIZE];
    #if (0u != CapSense_MULTIPLE_FREQUENCY_SET)
        extern const uint8 CapSense_senseClkDividerVal[CapSense_TOTAL_SCANSLOT_COUNT];
        extern const uint8 CapSense_sampleClkDividerVal[CapSense_TOTAL_SCANSLOT_COUNT];
    #else
        extern const uint8 CapSense_senseClkDividerVal;
        extern const uint8 CapSense_sampleClkDividerVal;
    #endif /* (0u != CapSense_MULTIPLE_FREQUENCY_SET) */
#endif /* (CapSense_TUNING_METHOD != CapSense__TUNING_NONE)  */

extern const uint8 CapSense_widgetNumber[CapSense_TOTAL_SENSOR_COUNT];

extern reg32* const CapSense_prtSelTbl[CapSense_CFG_REG_TBL_SIZE];
extern reg32* const CapSense_prtCfgTbl[CapSense_CFG_REG_TBL_SIZE];
extern reg32* const CapSense_prtDRTbl[CapSense_CFG_REG_TBL_SIZE];
extern reg32 * CapSense_pcTable[CapSense_PORT_PIN_CONFIG_TBL_ZISE];

extern const uint8  CapSense_portTable[CapSense_PORT_PIN_CONFIG_TBL_ZISE];
extern const uint32 CapSense_maskTable[CapSense_PORT_PIN_CONFIG_TBL_ZISE];
extern const uint8  CapSense_pinShiftTbl[CapSense_PORT_PIN_CONFIG_TBL_ZISE];

#if (0u != CapSense_INDEX_TABLE_SIZE)
extern const uint8 CYCODE CapSense_indexTable[CapSense_INDEX_TABLE_SIZE];
#endif /* (0u != CapSense_INDEX_TABLE_SIZE)) */

/***************************************************
*    Obsolete Names (will be removed in future)
***************************************************/
#define  CapSense_PrescalersTuningDone         CapSense_prescalersTuningDone
#define  CapSense_SensorRaw                    CapSense_sensorRaw
#define  CapSense_PRSResolutionTbl             CapSense_prsResolutionTbl
#define  CapSense_SensorEnableMask             CapSense_sensorEnableMask
#define  CapSense_Clk1DividerVal               CapSense_senseClkDividerVal
#define  CapSense_Clk2DividerVal               CapSense_sampleClkDividerVal
#define  CapSense_PrtSelTbl                    CapSense_prtSelTbl
#define  CapSense_PrtCfgTbl                    CapSense_prtCfgTbl
#define  CapSense_PrtDRTbl                     CapSense_prtDRTbl
#define  CapSense_idac1Settings                CapSense_modulationIDAC
#define  CapSense_idac2Settings                CapSense_compensationIDAC

#endif /* CY_CAPSENSE_CSD_CapSense_H */


 /* [] END OF FILE */
