spiricom/Electrobass_embedded/PSOC5_electrobass_stringsensors_fornextRev_largerpart/CE210514_PSOC3_5_Thermistor.cydsn/codegentemp/SPIM_2.h

/*******************************************************************************
* File Name: SPIM_2.h
* Version 2.50
*
* Description:
*  Contains the function prototypes, constants and register definition
*  of the SPI Master Component.
*
* Note:
*  None
*
********************************************************************************
* Copyright 2008-2015, Cypress Semiconductor Corporation.  All rights reserved.
* You may use this file only in accordance with the license, terms, conditions,
* disclaimers, and limitations in the end user license agreement accompanying
* the software package with which this file was provided.
*******************************************************************************/

#if !defined(CY_SPIM_SPIM_2_H)
#define CY_SPIM_SPIM_2_H

#include "cyfitter.h"
#include "cytypes.h"
#include "CyLib.h" /* For CyEnterCriticalSection() and CyExitCriticalSection() functions */


/***************************************
*   Conditional Compilation Parameters
***************************************/

#define SPIM_2_INTERNAL_CLOCK             (1u)

#if(0u != SPIM_2_INTERNAL_CLOCK)
    #include "SPIM_2_IntClock.h"
#endif /* (0u != SPIM_2_INTERNAL_CLOCK) */

#define SPIM_2_MODE                       (1u)
#define SPIM_2_DATA_WIDTH                 (8u)
#define SPIM_2_MODE_USE_ZERO              (1u)
#define SPIM_2_BIDIRECTIONAL_MODE         (0u)

/* Internal interrupt handling */
#define SPIM_2_TX_BUFFER_SIZE             (4u)
#define SPIM_2_RX_BUFFER_SIZE             (4u)
#define SPIM_2_INTERNAL_TX_INT_ENABLED    (0u)
#define SPIM_2_INTERNAL_RX_INT_ENABLED    (0u)

#define SPIM_2_SINGLE_REG_SIZE            (8u)
#define SPIM_2_USE_SECOND_DATAPATH        (SPIM_2_DATA_WIDTH > SPIM_2_SINGLE_REG_SIZE)

#define SPIM_2_FIFO_SIZE                  (4u)
#define SPIM_2_TX_SOFTWARE_BUF_ENABLED    ((0u != SPIM_2_INTERNAL_TX_INT_ENABLED) && \
                                                     (SPIM_2_TX_BUFFER_SIZE > SPIM_2_FIFO_SIZE))

#define SPIM_2_RX_SOFTWARE_BUF_ENABLED    ((0u != SPIM_2_INTERNAL_RX_INT_ENABLED) && \
                                                     (SPIM_2_RX_BUFFER_SIZE > SPIM_2_FIFO_SIZE))


/***************************************
*        Data Struct Definition
***************************************/

/* Sleep Mode API Support */
typedef struct
{
    uint8 enableState;
    uint8 cntrPeriod;
} SPIM_2_BACKUP_STRUCT;


/***************************************
*        Function Prototypes
***************************************/

void  SPIM_2_Init(void)                           ;
void  SPIM_2_Enable(void)                         ;
void  SPIM_2_Start(void)                          ;
void  SPIM_2_Stop(void)                           ;

void  SPIM_2_EnableTxInt(void)                    ;
void  SPIM_2_EnableRxInt(void)                    ;
void  SPIM_2_DisableTxInt(void)                   ;
void  SPIM_2_DisableRxInt(void)                   ;

void  SPIM_2_Sleep(void)                          ;
void  SPIM_2_Wakeup(void)                         ;
void  SPIM_2_SaveConfig(void)                     ;
void  SPIM_2_RestoreConfig(void)                  ;

void  SPIM_2_SetTxInterruptMode(uint8 intSrc)     ;
void  SPIM_2_SetRxInterruptMode(uint8 intSrc)     ;
uint8 SPIM_2_ReadTxStatus(void)                   ;
uint8 SPIM_2_ReadRxStatus(void)                   ;
void  SPIM_2_WriteTxData(uint8 txData)  \
                                                            ;
uint8 SPIM_2_ReadRxData(void) \
                                                            ;
uint8 SPIM_2_GetRxBufferSize(void)                ;
uint8 SPIM_2_GetTxBufferSize(void)                ;
void  SPIM_2_ClearRxBuffer(void)                  ;
void  SPIM_2_ClearTxBuffer(void)                  ;
void  SPIM_2_ClearFIFO(void)                              ;
void  SPIM_2_PutArray(const uint8 buffer[], uint8 byteCount) \
                                                            ;

#if(0u != SPIM_2_BIDIRECTIONAL_MODE)
    void  SPIM_2_TxEnable(void)                   ;
    void  SPIM_2_TxDisable(void)                  ;
#endif /* (0u != SPIM_2_BIDIRECTIONAL_MODE) */

CY_ISR_PROTO(SPIM_2_TX_ISR);
CY_ISR_PROTO(SPIM_2_RX_ISR);


/***************************************
*   Variable with external linkage
***************************************/

extern uint8 SPIM_2_initVar;


/***************************************
*           API Constants
***************************************/

#define SPIM_2_TX_ISR_NUMBER     ((uint8) (SPIM_2_TxInternalInterrupt__INTC_NUMBER))
#define SPIM_2_RX_ISR_NUMBER     ((uint8) (SPIM_2_RxInternalInterrupt__INTC_NUMBER))

#define SPIM_2_TX_ISR_PRIORITY   ((uint8) (SPIM_2_TxInternalInterrupt__INTC_PRIOR_NUM))
#define SPIM_2_RX_ISR_PRIORITY   ((uint8) (SPIM_2_RxInternalInterrupt__INTC_PRIOR_NUM))


/***************************************
*    Initial Parameter Constants
***************************************/

#define SPIM_2_INT_ON_SPI_DONE    ((uint8) (0u   << SPIM_2_STS_SPI_DONE_SHIFT))
#define SPIM_2_INT_ON_TX_EMPTY    ((uint8) (1u   << SPIM_2_STS_TX_FIFO_EMPTY_SHIFT))
#define SPIM_2_INT_ON_TX_NOT_FULL ((uint8) (0u << \
                                                                           SPIM_2_STS_TX_FIFO_NOT_FULL_SHIFT))
#define SPIM_2_INT_ON_BYTE_COMP   ((uint8) (0u  << SPIM_2_STS_BYTE_COMPLETE_SHIFT))
#define SPIM_2_INT_ON_SPI_IDLE    ((uint8) (0u   << SPIM_2_STS_SPI_IDLE_SHIFT))

/* Disable TX_NOT_FULL if software buffer is used */
#define SPIM_2_INT_ON_TX_NOT_FULL_DEF ((SPIM_2_TX_SOFTWARE_BUF_ENABLED) ? \
                                                                        (0u) : (SPIM_2_INT_ON_TX_NOT_FULL))

/* TX interrupt mask */
#define SPIM_2_TX_INIT_INTERRUPTS_MASK    (SPIM_2_INT_ON_SPI_DONE  | \
                                                     SPIM_2_INT_ON_TX_EMPTY  | \
                                                     SPIM_2_INT_ON_TX_NOT_FULL_DEF | \
                                                     SPIM_2_INT_ON_BYTE_COMP | \
                                                     SPIM_2_INT_ON_SPI_IDLE)

#define SPIM_2_INT_ON_RX_FULL         ((uint8) (0u << \
                                                                          SPIM_2_STS_RX_FIFO_FULL_SHIFT))
#define SPIM_2_INT_ON_RX_NOT_EMPTY    ((uint8) (1u << \
                                                                          SPIM_2_STS_RX_FIFO_NOT_EMPTY_SHIFT))
#define SPIM_2_INT_ON_RX_OVER         ((uint8) (0u << \
                                                                          SPIM_2_STS_RX_FIFO_OVERRUN_SHIFT))

/* RX interrupt mask */
#define SPIM_2_RX_INIT_INTERRUPTS_MASK    (SPIM_2_INT_ON_RX_FULL      | \
                                                     SPIM_2_INT_ON_RX_NOT_EMPTY | \
                                                     SPIM_2_INT_ON_RX_OVER)
/* Nubmer of bits to receive/transmit */
#define SPIM_2_BITCTR_INIT            (((uint8) (SPIM_2_DATA_WIDTH << 1u)) - 1u)


/***************************************
*             Registers
***************************************/
#if(CY_PSOC3 || CY_PSOC5)
    #define SPIM_2_TXDATA_REG (* (reg8 *) \
                                                SPIM_2_BSPIM_sR8_Dp_u0__F0_REG)
    #define SPIM_2_TXDATA_PTR (  (reg8 *) \
                                                SPIM_2_BSPIM_sR8_Dp_u0__F0_REG)
    #define SPIM_2_RXDATA_REG (* (reg8 *) \
                                                SPIM_2_BSPIM_sR8_Dp_u0__F1_REG)
    #define SPIM_2_RXDATA_PTR (  (reg8 *) \
                                                SPIM_2_BSPIM_sR8_Dp_u0__F1_REG)
#else   /* PSOC4 */
    #if(SPIM_2_USE_SECOND_DATAPATH)
        #define SPIM_2_TXDATA_REG (* (reg16 *) \
                                          SPIM_2_BSPIM_sR8_Dp_u0__16BIT_F0_REG)
        #define SPIM_2_TXDATA_PTR (  (reg16 *) \
                                          SPIM_2_BSPIM_sR8_Dp_u0__16BIT_F0_REG)
        #define SPIM_2_RXDATA_REG (* (reg16 *) \
                                          SPIM_2_BSPIM_sR8_Dp_u0__16BIT_F1_REG)
        #define SPIM_2_RXDATA_PTR (  (reg16 *) \
                                          SPIM_2_BSPIM_sR8_Dp_u0__16BIT_F1_REG)
    #else
        #define SPIM_2_TXDATA_REG (* (reg8 *) \
                                                SPIM_2_BSPIM_sR8_Dp_u0__F0_REG)
        #define SPIM_2_TXDATA_PTR (  (reg8 *) \
                                                SPIM_2_BSPIM_sR8_Dp_u0__F0_REG)
        #define SPIM_2_RXDATA_REG (* (reg8 *) \
                                                SPIM_2_BSPIM_sR8_Dp_u0__F1_REG)
        #define SPIM_2_RXDATA_PTR (  (reg8 *) \
                                                SPIM_2_BSPIM_sR8_Dp_u0__F1_REG)
    #endif /* (SPIM_2_USE_SECOND_DATAPATH) */
#endif     /* (CY_PSOC3 || CY_PSOC5) */

#define SPIM_2_AUX_CONTROL_DP0_REG (* (reg8 *) \
                                        SPIM_2_BSPIM_sR8_Dp_u0__DP_AUX_CTL_REG)
#define SPIM_2_AUX_CONTROL_DP0_PTR (  (reg8 *) \
                                        SPIM_2_BSPIM_sR8_Dp_u0__DP_AUX_CTL_REG)

#if(SPIM_2_USE_SECOND_DATAPATH)
    #define SPIM_2_AUX_CONTROL_DP1_REG  (* (reg8 *) \
                                        SPIM_2_BSPIM_sR8_Dp_u1__DP_AUX_CTL_REG)
    #define SPIM_2_AUX_CONTROL_DP1_PTR  (  (reg8 *) \
                                        SPIM_2_BSPIM_sR8_Dp_u1__DP_AUX_CTL_REG)
#endif /* (SPIM_2_USE_SECOND_DATAPATH) */

#define SPIM_2_COUNTER_PERIOD_REG     (* (reg8 *) SPIM_2_BSPIM_BitCounter__PERIOD_REG)
#define SPIM_2_COUNTER_PERIOD_PTR     (  (reg8 *) SPIM_2_BSPIM_BitCounter__PERIOD_REG)
#define SPIM_2_COUNTER_CONTROL_REG    (* (reg8 *) SPIM_2_BSPIM_BitCounter__CONTROL_AUX_CTL_REG)
#define SPIM_2_COUNTER_CONTROL_PTR    (  (reg8 *) SPIM_2_BSPIM_BitCounter__CONTROL_AUX_CTL_REG)

#define SPIM_2_TX_STATUS_REG          (* (reg8 *) SPIM_2_BSPIM_TxStsReg__STATUS_REG)
#define SPIM_2_TX_STATUS_PTR          (  (reg8 *) SPIM_2_BSPIM_TxStsReg__STATUS_REG)
#define SPIM_2_RX_STATUS_REG          (* (reg8 *) SPIM_2_BSPIM_RxStsReg__STATUS_REG)
#define SPIM_2_RX_STATUS_PTR          (  (reg8 *) SPIM_2_BSPIM_RxStsReg__STATUS_REG)

#define SPIM_2_CONTROL_REG            (* (reg8 *) \
                                      SPIM_2_BSPIM_BidirMode_CtrlReg__CONTROL_REG)
#define SPIM_2_CONTROL_PTR            (  (reg8 *) \
                                      SPIM_2_BSPIM_BidirMode_CtrlReg__CONTROL_REG)

#define SPIM_2_TX_STATUS_MASK_REG     (* (reg8 *) SPIM_2_BSPIM_TxStsReg__MASK_REG)
#define SPIM_2_TX_STATUS_MASK_PTR     (  (reg8 *) SPIM_2_BSPIM_TxStsReg__MASK_REG)
#define SPIM_2_RX_STATUS_MASK_REG     (* (reg8 *) SPIM_2_BSPIM_RxStsReg__MASK_REG)
#define SPIM_2_RX_STATUS_MASK_PTR     (  (reg8 *) SPIM_2_BSPIM_RxStsReg__MASK_REG)

#define SPIM_2_TX_STATUS_ACTL_REG     (* (reg8 *) SPIM_2_BSPIM_TxStsReg__STATUS_AUX_CTL_REG)
#define SPIM_2_TX_STATUS_ACTL_PTR     (  (reg8 *) SPIM_2_BSPIM_TxStsReg__STATUS_AUX_CTL_REG)
#define SPIM_2_RX_STATUS_ACTL_REG     (* (reg8 *) SPIM_2_BSPIM_RxStsReg__STATUS_AUX_CTL_REG)
#define SPIM_2_RX_STATUS_ACTL_PTR     (  (reg8 *) SPIM_2_BSPIM_RxStsReg__STATUS_AUX_CTL_REG)

#if(SPIM_2_USE_SECOND_DATAPATH)
    #define SPIM_2_AUX_CONTROLDP1     (SPIM_2_AUX_CONTROL_DP1_REG)
#endif /* (SPIM_2_USE_SECOND_DATAPATH) */


/***************************************
*       Register Constants
***************************************/

/* Status Register Definitions */
#define SPIM_2_STS_SPI_DONE_SHIFT             (0x00u)
#define SPIM_2_STS_TX_FIFO_EMPTY_SHIFT        (0x01u)
#define SPIM_2_STS_TX_FIFO_NOT_FULL_SHIFT     (0x02u)
#define SPIM_2_STS_BYTE_COMPLETE_SHIFT        (0x03u)
#define SPIM_2_STS_SPI_IDLE_SHIFT             (0x04u)
#define SPIM_2_STS_RX_FIFO_FULL_SHIFT         (0x04u)
#define SPIM_2_STS_RX_FIFO_NOT_EMPTY_SHIFT    (0x05u)
#define SPIM_2_STS_RX_FIFO_OVERRUN_SHIFT      (0x06u)

#define SPIM_2_STS_SPI_DONE           ((uint8) (0x01u << SPIM_2_STS_SPI_DONE_SHIFT))
#define SPIM_2_STS_TX_FIFO_EMPTY      ((uint8) (0x01u << SPIM_2_STS_TX_FIFO_EMPTY_SHIFT))
#define SPIM_2_STS_TX_FIFO_NOT_FULL   ((uint8) (0x01u << SPIM_2_STS_TX_FIFO_NOT_FULL_SHIFT))
#define SPIM_2_STS_BYTE_COMPLETE      ((uint8) (0x01u << SPIM_2_STS_BYTE_COMPLETE_SHIFT))
#define SPIM_2_STS_SPI_IDLE           ((uint8) (0x01u << SPIM_2_STS_SPI_IDLE_SHIFT))
#define SPIM_2_STS_RX_FIFO_FULL       ((uint8) (0x01u << SPIM_2_STS_RX_FIFO_FULL_SHIFT))
#define SPIM_2_STS_RX_FIFO_NOT_EMPTY  ((uint8) (0x01u << SPIM_2_STS_RX_FIFO_NOT_EMPTY_SHIFT))
#define SPIM_2_STS_RX_FIFO_OVERRUN    ((uint8) (0x01u << SPIM_2_STS_RX_FIFO_OVERRUN_SHIFT))

/* TX and RX masks for clear on read bits */
#define SPIM_2_TX_STS_CLR_ON_RD_BYTES_MASK    (0x09u)
#define SPIM_2_RX_STS_CLR_ON_RD_BYTES_MASK    (0x40u)

/* StatusI Register Interrupt Enable Control Bits */
/* As defined by the Register map for the AUX Control Register */
#define SPIM_2_INT_ENABLE     (0x10u) /* Enable interrupt from statusi */
#define SPIM_2_TX_FIFO_CLR    (0x01u) /* F0 - TX FIFO */
#define SPIM_2_RX_FIFO_CLR    (0x02u) /* F1 - RX FIFO */
#define SPIM_2_FIFO_CLR       (SPIM_2_TX_FIFO_CLR | SPIM_2_RX_FIFO_CLR)

/* Bit Counter (7-bit) Control Register Bit Definitions */
/* As defined by the Register map for the AUX Control Register */
#define SPIM_2_CNTR_ENABLE    (0x20u) /* Enable CNT7 */

/* Bi-Directional mode control bit */
#define SPIM_2_CTRL_TX_SIGNAL_EN  (0x01u)

/* Datapath Auxillary Control Register definitions */
#define SPIM_2_AUX_CTRL_FIFO0_CLR         (0x01u)
#define SPIM_2_AUX_CTRL_FIFO1_CLR         (0x02u)
#define SPIM_2_AUX_CTRL_FIFO0_LVL         (0x04u)
#define SPIM_2_AUX_CTRL_FIFO1_LVL         (0x08u)
#define SPIM_2_STATUS_ACTL_INT_EN_MASK    (0x10u)

/* Component disabled */
#define SPIM_2_DISABLED   (0u)


/***************************************
*       Macros
***************************************/

/* Returns true if componentn enabled */
#define SPIM_2_IS_ENABLED (0u != (SPIM_2_TX_STATUS_ACTL_REG & SPIM_2_INT_ENABLE))

/* Retuns TX status register */
#define SPIM_2_GET_STATUS_TX(swTxSts) ( (uint8)(SPIM_2_TX_STATUS_REG | \
                                                          ((swTxSts) & SPIM_2_TX_STS_CLR_ON_RD_BYTES_MASK)) )
/* Retuns RX status register */
#define SPIM_2_GET_STATUS_RX(swRxSts) ( (uint8)(SPIM_2_RX_STATUS_REG | \
                                                          ((swRxSts) & SPIM_2_RX_STS_CLR_ON_RD_BYTES_MASK)) )


/***************************************
* The following code is DEPRECATED and 
* should not be used in new projects.
***************************************/

#define SPIM_2_WriteByte   SPIM_2_WriteTxData
#define SPIM_2_ReadByte    SPIM_2_ReadRxData
void  SPIM_2_SetInterruptMode(uint8 intSrc)       ;
uint8 SPIM_2_ReadStatus(void)                     ;
void  SPIM_2_EnableInt(void)                      ;
void  SPIM_2_DisableInt(void)                     ;

#define SPIM_2_TXDATA                 (SPIM_2_TXDATA_REG)
#define SPIM_2_RXDATA                 (SPIM_2_RXDATA_REG)
#define SPIM_2_AUX_CONTROLDP0         (SPIM_2_AUX_CONTROL_DP0_REG)
#define SPIM_2_TXBUFFERREAD           (SPIM_2_txBufferRead)
#define SPIM_2_TXBUFFERWRITE          (SPIM_2_txBufferWrite)
#define SPIM_2_RXBUFFERREAD           (SPIM_2_rxBufferRead)
#define SPIM_2_RXBUFFERWRITE          (SPIM_2_rxBufferWrite)

#define SPIM_2_COUNTER_PERIOD         (SPIM_2_COUNTER_PERIOD_REG)
#define SPIM_2_COUNTER_CONTROL        (SPIM_2_COUNTER_CONTROL_REG)
#define SPIM_2_STATUS                 (SPIM_2_TX_STATUS_REG)
#define SPIM_2_CONTROL                (SPIM_2_CONTROL_REG)
#define SPIM_2_STATUS_MASK            (SPIM_2_TX_STATUS_MASK_REG)
#define SPIM_2_STATUS_ACTL            (SPIM_2_TX_STATUS_ACTL_REG)

#define SPIM_2_INIT_INTERRUPTS_MASK  (SPIM_2_INT_ON_SPI_DONE     | \
                                                SPIM_2_INT_ON_TX_EMPTY     | \
                                                SPIM_2_INT_ON_TX_NOT_FULL_DEF  | \
                                                SPIM_2_INT_ON_RX_FULL      | \
                                                SPIM_2_INT_ON_RX_NOT_EMPTY | \
                                                SPIM_2_INT_ON_RX_OVER      | \
                                                SPIM_2_INT_ON_BYTE_COMP)
                                                
#define SPIM_2_DataWidth                  (SPIM_2_DATA_WIDTH)
#define SPIM_2_InternalClockUsed          (SPIM_2_INTERNAL_CLOCK)
#define SPIM_2_InternalTxInterruptEnabled (SPIM_2_INTERNAL_TX_INT_ENABLED)
#define SPIM_2_InternalRxInterruptEnabled (SPIM_2_INTERNAL_RX_INT_ENABLED)
#define SPIM_2_ModeUseZero                (SPIM_2_MODE_USE_ZERO)
#define SPIM_2_BidirectionalMode          (SPIM_2_BIDIRECTIONAL_MODE)
#define SPIM_2_Mode                       (SPIM_2_MODE)
#define SPIM_2_DATAWIDHT                  (SPIM_2_DATA_WIDTH)
#define SPIM_2_InternalInterruptEnabled   (0u)

#define SPIM_2_TXBUFFERSIZE   (SPIM_2_TX_BUFFER_SIZE)
#define SPIM_2_RXBUFFERSIZE   (SPIM_2_RX_BUFFER_SIZE)

#define SPIM_2_TXBUFFER       SPIM_2_txBuffer
#define SPIM_2_RXBUFFER       SPIM_2_rxBuffer

#endif /* (CY_SPIM_SPIM_2_H) */


/* [] END OF FILE */
