spiricom/Electrobass_embedded/PSOC5_electrobass_stringsensors_fornextRev_largerpart/CE210514_PSOC3_5_Thermistor.cydsn/codegentemp/CapSense_IdacCH1.h

/*******************************************************************************
* File Name: CapSense_IdacCH1.c
* Version 2.0
*
* Description:
*  This file contains the function prototypes and constants used in
*  the 8-bit Current DAC (IDAC8) User Module.
*
* Note:
*  None
*
********************************************************************************
* Copyright 2008-2012, Cypress Semiconductor Corporation.  All rights reserved.
* You may use this file only in accordance with the license, terms, conditions, 
* disclaimers, and limitations in the end user license agreement accompanying 
* the software package with which this file was provided.
*******************************************************************************/

#if !defined(CY_IDAC8_CapSense_IdacCH1_H)  
#define CY_IDAC8_CapSense_IdacCH1_H

#include "cyfitter.h"
#include "cytypes.h"

/* Check to see if required defines such as CY_PSOC5LP are available */
/* They are defined starting with cy_boot v3.0 */
#if !defined (CY_PSOC5LP)
    #error Component IDAC8_v2_0 requires cy_boot v3.0 or later
#endif /* (CY_PSOC5LP) */


/***************************************
*       Type defines
***************************************/

/* Sleep Mode API Support */
typedef struct
{
    uint8 enableState;
    uint8 data_value;
}CapSense_IdacCH1_backupStruct;


#if (CY_PSOC5A)
    /* Stop API changes for PSoC5A */
    typedef struct
    {
        uint8 DACCR0Reg;
    }   CapSense_IdacCH1_LOWPOWER_BACKUP_STRUCT;
#endif /* CY_PSOC5A */

/* component init state */
extern uint8 CapSense_IdacCH1_initVar;


/***************************************
*        Function Prototypes 
***************************************/

void    CapSense_IdacCH1_Start(void)                 ;
void    CapSense_IdacCH1_Stop(void)                  ;
void    CapSense_IdacCH1_SetSpeed(uint8 speed)       ;
void    CapSense_IdacCH1_SetPolarity(uint8 polarity) ;
void    CapSense_IdacCH1_SetRange(uint8 range)      ;
void    CapSense_IdacCH1_SetValue(uint8 value)       ;
void    CapSense_IdacCH1_DacTrim(void)               ;

/* Sleep Retention APIs */
void CapSense_IdacCH1_Init(void)                     ;
void CapSense_IdacCH1_Enable(void)                   ;
void CapSense_IdacCH1_SaveConfig(void)               ;
void CapSense_IdacCH1_RestoreConfig(void)            ;
void CapSense_IdacCH1_Sleep(void)                    ;
void CapSense_IdacCH1_Wakeup(void)                   ;


/***************************************
*       Paramater Initial Values
***************************************/

#define CapSense_IdacCH1_DEFAULT_RANGE     4u                                   /* Default DAC range */
#define CapSense_IdacCH1_DEFAULT_SPEED     ((uint8)(((0u != 0u) ? 1u : 0u) << 1u))   /* Default DAC speed */
#define CapSense_IdacCH1_DEFAULT_CNTL      0x00u                                            /* Default Control */
#define CapSense_IdacCH1_DEFAULT_STRB     0u                                   /* Default Strobe mode */
#define CapSense_IdacCH1_DEFAULT_DATA     0u                                 /* Initial DAC value */
#define CapSense_IdacCH1_DEFAULT_POLARITY 4u                                      /* Default Sink or Source */
#define CapSense_IdacCH1_DEFAULT_DATA_SRC 0u                                   /* Default Data Source */   
#define CapSense_IdacCH1_HARDWARE_ENABLE  1u                               /*Hardware Enable */


/***************************************
*              API Constants        
***************************************/

/* SetRange constants */

#define CapSense_IdacCH1_RANGE_32uA             (0x00u)
#define CapSense_IdacCH1_RANGE_255uA            (0x04u)
#define CapSense_IdacCH1_RANGE_2mA              (0x08u)

/* SetPolarity constants */
#define CapSense_IdacCH1_SOURCE                 (0x00u)
#define CapSense_IdacCH1_SINK                   (0x04u)
#define CapSense_IdacCH1_HARDWARE_CONTROLLED    (0x02u)

/* Power setting for SetSpeed API  */
#define CapSense_IdacCH1_LOWSPEED               (0x00u)
#define CapSense_IdacCH1_HIGHSPEED              (0x02u)


/***************************************
*              Registers        
***************************************/
#define CapSense_IdacCH1_CR0_REG         (* (reg8 *) CapSense_IdacCH1_viDAC8__CR0 )
#define CapSense_IdacCH1_CR0_PTR         (  (reg8 *) CapSense_IdacCH1_viDAC8__CR0 )
#define CapSense_IdacCH1_CR1_REG         (* (reg8 *) CapSense_IdacCH1_viDAC8__CR1 )
#define CapSense_IdacCH1_CR1_PTR         (  (reg8 *) CapSense_IdacCH1_viDAC8__CR1 )
#define CapSense_IdacCH1_Data_REG        (* (reg8 *) CapSense_IdacCH1_viDAC8__D )
#define CapSense_IdacCH1_Data_PTR        (  (reg8 *) CapSense_IdacCH1_viDAC8__D )
#define CapSense_IdacCH1_Strobe_REG      (* (reg8 *) CapSense_IdacCH1_viDAC8__STROBE )
#define CapSense_IdacCH1_Strobe_PTR      (  (reg8 *) CapSense_IdacCH1_viDAC8__STROBE )
#define CapSense_IdacCH1_SW0_REG         (* (reg8 *) CapSense_IdacCH1_viDAC8__SW0 )
#define CapSense_IdacCH1_SW0_PTR         (  (reg8 *) CapSense_IdacCH1_viDAC8__SW0 )
#define CapSense_IdacCH1_SW2_REG         (* (reg8 *) CapSense_IdacCH1_viDAC8__SW2 )
#define CapSense_IdacCH1_SW2_PTR         (  (reg8 *) CapSense_IdacCH1_viDAC8__SW2 )
#define CapSense_IdacCH1_SW3_REG         (* (reg8 *) CapSense_IdacCH1_viDAC8__SW3 )
#define CapSense_IdacCH1_SW3_PTR         (  (reg8 *) CapSense_IdacCH1_viDAC8__SW3 )
#define CapSense_IdacCH1_SW4_REG         (* (reg8 *) CapSense_IdacCH1_viDAC8__SW4 )
#define CapSense_IdacCH1_SW4_PTR         (  (reg8 *) CapSense_IdacCH1_viDAC8__SW4 )
#define CapSense_IdacCH1_TR_REG          (* (reg8 *) CapSense_IdacCH1_viDAC8__TR )
#define CapSense_IdacCH1_TR_PTR          (  (reg8 *) CapSense_IdacCH1_viDAC8__TR )
#define CapSense_IdacCH1_PWRMGR_REG      (* (reg8 *) CapSense_IdacCH1_viDAC8__PM_ACT_CFG )  /* Power manager */
#define CapSense_IdacCH1_PWRMGR_PTR      (  (reg8 *) CapSense_IdacCH1_viDAC8__PM_ACT_CFG )  /* Power manager */
#define CapSense_IdacCH1_STBY_PWRMGR_REG (* (reg8 *) CapSense_IdacCH1_viDAC8__PM_STBY_CFG )  /* Standby Power manager */
#define CapSense_IdacCH1_STBY_PWRMGR_PTR (  (reg8 *) CapSense_IdacCH1_viDAC8__PM_STBY_CFG )  /* Standby Power manager */

/***************************************
*  Registers definitions
* for backward capability        
***************************************/
#define CapSense_IdacCH1_CR0         (* (reg8 *) CapSense_IdacCH1_viDAC8__CR0 )
#define CapSense_IdacCH1_CR1         (* (reg8 *) CapSense_IdacCH1_viDAC8__CR1 )
#define CapSense_IdacCH1_Data        (* (reg8 *) CapSense_IdacCH1_viDAC8__D )
#define CapSense_IdacCH1_Data_PTR    (  (reg8 *) CapSense_IdacCH1_viDAC8__D )
#define CapSense_IdacCH1_Strobe      (* (reg8 *) CapSense_IdacCH1_viDAC8__STROBE )
#define CapSense_IdacCH1_SW0         (* (reg8 *) CapSense_IdacCH1_viDAC8__SW0 )
#define CapSense_IdacCH1_SW2         (* (reg8 *) CapSense_IdacCH1_viDAC8__SW2 )
#define CapSense_IdacCH1_SW3         (* (reg8 *) CapSense_IdacCH1_viDAC8__SW3 )
#define CapSense_IdacCH1_SW4         (* (reg8 *) CapSense_IdacCH1_viDAC8__SW4 )
#define CapSense_IdacCH1_TR          (* (reg8 *) CapSense_IdacCH1_viDAC8__TR )
#define CapSense_IdacCH1_PWRMGR      (* (reg8 *) CapSense_IdacCH1_viDAC8__PM_ACT_CFG )  /* Power manager */
#define CapSense_IdacCH1_STBY_PWRMGR (* (reg8 *) CapSense_IdacCH1_viDAC8__PM_STBY_CFG )  /* Standby Power manager */


/******************************************************************************
*              Trim    
*
* Note - VIDAC trim values are stored in the "Customer Table" area in 
* Row 1 of the Hidden Flash.  There are 8 bytes of trim data for each VIDAC 
* block.
* The values are:
*       I Gain offset, min range, Sourcing
*       I Gain offset, min range, Sinking
*       I Gain offset, med range, Sourcing
*       I Gain offset, med range, Sinking
*       I Gain offset, max range, Sourcing
*       I Gain offset, max range, Sinking
*       V Gain offset, 1V range
*       V Gain offset, 4V range
*
* The data set for the 4 VIDACs are arranged using a left side/right 
* side approach:
*  Left 0, Left 1, Right 0, Right 1.
* When mapped to the VIDAC0 thru VIDAC3 as:
*  VIDAC 0, VIDAC 2, VIDAC 1, VIDAC 3
******************************************************************************/

#define CapSense_IdacCH1_DAC_TRIM_BASE   CapSense_IdacCH1_viDAC8__TRIM__M1


/***************************************
*         Register Constants       
***************************************/

/* CR0 iDAC Control Register 0 definitions */  

/* Bit Field  DAC_HS_MODE                  */
#define CapSense_IdacCH1_HS_MASK        (0x02u)
#define CapSense_IdacCH1_HS_LOWPOWER    (0x00u)
#define CapSense_IdacCH1_HS_HIGHSPEED   (0x02u)

/* Bit Field  DAC_MODE                  */
#define CapSense_IdacCH1_MODE_MASK      (0x10u)
#define CapSense_IdacCH1_MODE_V         (0x00u)
#define CapSense_IdacCH1_MODE_I         (0x10u)

/* Bit Field  DAC_RANGE                  */
#define CapSense_IdacCH1_RANGE_MASK     (0x0Cu)
#define CapSense_IdacCH1_RANGE_0        (0x00u)
#define CapSense_IdacCH1_RANGE_1        (0x04u)
#define CapSense_IdacCH1_RANGE_2        (0x08u)
#define CapSense_IdacCH1_RANGE_3        (0x0Cu)

/* CR1 iDAC Control Register 1 definitions */

/* Bit Field  DAC_MX_DATA                  */
#define CapSense_IdacCH1_SRC_MASK       (0x20u)
#define CapSense_IdacCH1_SRC_REG        (0x00u)
#define CapSense_IdacCH1_SRC_UDB        (0x20u)

/* This bit enable reset from UDB array      */
#define CapSense_IdacCH1_RESET_MASK     (0x10u)
#define CapSense_IdacCH1_RESET_ENABLE   (0x10u)
#define CapSense_IdacCH1_RESET_DISABLE  (0x00u)

/* Bit Field  DAC_MX_IDIR_SRC              */
#define CapSense_IdacCH1_IDIR_SRC_MASK  (0x08u)
#define CapSense_IdacCH1_IDIR_SRC_REG   (0x00u)
#define CapSense_IdacCH1_IDIR_SRC_UDB   (0x08u)

/* Bit Field  DAC_I_DIR                  */
/* Register control of current direction      */
#define CapSense_IdacCH1_IDIR_MASK      (0x04u)
#define CapSense_IdacCH1_IDIR_SRC       (0x00u)
#define CapSense_IdacCH1_IDIR_SINK      (0x04u)

/* Bit Field  DAC_MX_IOFF_SRC                  */
/* Selects source of IOFF control, reg or UDB  */
#define CapSense_IdacCH1_IDIR_CTL_MASK  (0x02u)
#define CapSense_IdacCH1_IDIR_CTL_REG   (0x00u)
#define CapSense_IdacCH1_IDIR_CTL_UDB   (0x02u)

/* Bit Field  DAC_MX_IOFF                   */
/* Register control of IDAC                 */
/* Only valid if IOFF CTL is set to Reg     */
#define CapSense_IdacCH1_I_OFF_MASK     (0x01u)
#define CapSense_IdacCH1_I_OFF          (0x00u)
#define CapSense_IdacCH1_I_ON           (0x01u)

/* This bit enables data from DAC bus      */
#define CapSense_IdacCH1_DACBUS_MASK    (0x20u)
#define CapSense_IdacCH1_DACBUS_ENABLE  (0x20u)
#define CapSense_IdacCH1_DACBUS_DISABLE (0x00u)

/* DAC STROBE Strobe Control Register definitions */

/* Bit Field  DAC_MX_STROBE                  */
#define CapSense_IdacCH1_STRB_MASK      (0x08u)
#define CapSense_IdacCH1_STRB_EN        (0x08u)
#define CapSense_IdacCH1_STRB_DIS       (0x00u)

/* PM_ACT_CFG (Active Power Mode CFG Register)     */ 
#define CapSense_IdacCH1_ACT_PWR_EN   CapSense_IdacCH1_viDAC8__PM_ACT_MSK  /* Power enable mask */ 
#define CapSense_IdacCH1_STBY_PWR_EN  CapSense_IdacCH1_viDAC8__PM_STBY_MSK  /* Standby Power enable mask */ 

#endif /* CY_IDAC8_CapSense_IdacCH1_H */


/* [] END OF FILE */
