spiricom/Electrobass_embedded/PSOC5_electrobass_stringsensors_fornextRev_largerpart/CE210514_PSOC3_5_Thermistor.cydsn/codegentemp/USB.c

/***************************************************************************//**
* \file USB.c
* \version 3.20
*
* \brief
*  This file contains the global USBFS API functions.
*
* Note:
*  Many of the functions use an endpoint number. SRAM arrays are sized with 9
*  elements, so they are indexed directly by epNumber.  The SIE and ARB
*  registers are indexed by variations of epNumber - 1.
*
********************************************************************************
* \copyright
* Copyright 2008-2016, Cypress Semiconductor Corporation.  All rights reserved.
* You may use this file only in accordance with the license, terms, conditions,
* disclaimers, and limitations in the end user license agreement accompanying
* the software package with which this file was provided.
*******************************************************************************/

#include "USB_pvt.h"
#include "USB_cydmac.h"
#include "USB_hid.h"
#include "USB_Dp.h"


/***************************************
* Global data allocation
***************************************/

/** Indicates whether the USBFS has been initialized. The variable is
* initialized to 0 after device reset and set to 1 the first time USBFS_Start()
* is called. This allows the Component to restart without reinitialization after
* the first call to the USBFS_Start() routine.
* If re-initialization of the Component is required, the variable should be set
* to 0 before the USBFS_Start() routine is called. Alternatively, the USBFS can
* be reinitialized by calling both USBFS_Init() and USBFS_InitComponent()
* functions.
*/
uint8 USB_initVar = 0u;

#if (USB_EP_MANAGEMENT_DMA)
    #if (CY_PSOC4)
        static void USB_InitEpDma(void);

        /* DMA chanels assigend for endpoints. */
        const uint8 USB_DmaChan[USB_MAX_EP] =
        {
            0u,
            (uint8) USB_ep1_dma_CHANNEL,
            (uint8) USB_ep2_dma_CHANNEL,
            0u,
            0u,
            0u,
            0u,
            0u,
            0u,
        };        
    #else
        /* DMA chanels assigend for endpoints. */
        uint8 USB_DmaChan[USB_MAX_EP];
        
        /* DMA TDs require for PSoC 3/5LP operation. */
        uint8 USB_DmaTd[USB_MAX_EP];
    #endif /* (CY_PSOC4) */
#endif /* (USB_EP_MANAGEMENT_DMA) */

#if (USB_EP_MANAGEMENT_DMA_AUTO)
#if (CY_PSOC4)
    /* Number of DMA bursts. */
    uint8  USB_DmaEpBurstCnt   [USB_MAX_EP];
    
    /* Number of bytes to transfer in last DMA burst. */
    uint8  USB_DmaEpLastBurstEl[USB_MAX_EP];

    /* Storage for arrays above. */
    uint8  USB_DmaEpBurstCntBackup  [USB_MAX_EP];
    uint32 USB_DmaEpBufferAddrBackup[USB_MAX_EP];
     
    /* DMA trigger mux output for usb.dma_req[0-7]. */
    const uint8 USB_DmaReqOut[USB_MAX_EP] =
    {
        0u,
        USB_ep1_dma__TR_OUTPUT,
        USB_ep2_dma__TR_OUTPUT,
        0u,
        0u,
        0u,
        0u,
        0u,
        0u,
    };

    /* DMA trigger mux output for usb.dma_burstend[0-7]. */
    const uint8 USB_DmaBurstEndOut[USB_MAX_EP] =
    {
        0u,
        USB_BURSTEND_0_TR_OUTPUT,
        USB_BURSTEND_1_TR_OUTPUT,
        USB_BURSTEND_2_TR_OUTPUT,
        USB_BURSTEND_3_TR_OUTPUT,
        USB_BURSTEND_4_TR_OUTPUT,
        USB_BURSTEND_5_TR_OUTPUT,
        USB_BURSTEND_6_TR_OUTPUT,
        USB_BURSTEND_7_TR_OUTPUT
    };
    
#else
    #if (USB_EP_DMA_AUTO_OPT == 0u)
        static uint8 clearInDataRdyStatus = USB_ARB_EPX_CFG_DEFAULT;
        uint8 USB_DmaNextTd[USB_MAX_EP];
        const uint8 USB_epX_TD_TERMOUT_EN[USB_MAX_EP] =
        {
            0u,
            USB_ep1__TD_TERMOUT_EN,
            USB_ep2__TD_TERMOUT_EN,
            0u,
            0u,
            0u,
            0u,
            0u,
            0u,
        };

        volatile uint16 USB_inLength[USB_MAX_EP];
        const uint8 *USB_inDataPointer[USB_MAX_EP];
        volatile uint8 USB_inBufFull[USB_MAX_EP];
    #endif /* (USB_EP_DMA_AUTO_OPT == 0u) */
#endif /* (CY_PSOC4) */
#endif /* (USB_EP_MANAGEMENT_DMA_AUTO) */


/*******************************************************************************
* Function Name: USB_Start
****************************************************************************//**
*
*   This function performs all required initialization for the USBFS component.
*   After this function call, the USB device initiates communication with the
*   host by pull-up D+ line. This is the preferred method to begin component
*   operation.
*
*   Note that global interrupts have to be enabled because interrupts are
*   required for USBFS component operation.
*
*   PSoC 4200L devices: when USBFS component configured to DMA with Automatic
*   Buffer Management, the DMA interrupt priority is changed to the highest
*   (priority 0) inside this function.
*
*   PSoC 3/PSoC 5LP devices: when USBFS component configured to DMA with
*   Automatic Buffer Management, the Arbiter interrupt priority is changed to
*   the highest (priority 0) inside this function.
*
*  \param device
*          Contains the device number of the desired device descriptor.
*          The device number can be found in the Device Descriptor Tab of
*          "Configure" dialog, under the settings of desired Device Descriptor,
*          in the "Device Number" field.
*  \param mode:
*   The operating voltage. This determines whether the voltage regulator
*   is enabled for 5V operation or if pass through mode is used for 3.3V
*   operation. Symbolic names and their associated values are given in the
*   following list.
*
*       *USB_3V_OPERATION* - Disable voltage regulator and pass-
*                                      through Vcc for pull-up
*
*       *USB_5V_OPERATION* - Enable voltage regulator and use
*                                      regulator for pull-up
*
*       *USB_DWR_POWER_OPERATION* - Enable or disable the voltage
*                                      regulator depending on the power supply
*                                      voltage configuration in the DWR tab.
*                                      For PSoC 3/5LP devices, the VDDD supply
*                                      voltage is considered and for PSoC 4A-L,
*                                      the VBUS supply voltage is considered.*
* \globalvars
*  \ref USB_initVar
*
* \sideeffect
*   This function will reset all communication states to default.
*
* \reentrant
*  No.
*
*******************************************************************************/
void USB_Start(uint8 device, uint8 mode) 
{
    if (0u == USB_initVar)
    {
        USB_Init();
        USB_initVar = 1u;
    }

    USB_InitComponent(device, mode);
}


/*******************************************************************************
* Function Name: USB_Init
****************************************************************************//**
*
* This function initializes or restores the component according to the
* customizer Configure dialog settings. It is not necessary to call
* USB_Init() because the USB_Start() routine calls
* this function and is the preferred method to begin component operation.
*
* \reentrant
*  No.
*
*******************************************************************************/
void USB_Init(void) 
{
#if (CY_PSOC4)
    /* Enable clock to USB IP. */
    USB_USB_CLK_EN_REG = USB_USB_CLK_CSR_CLK_EN;

    /* The internal regulator (CR1.REG_ENABLE) is enabled in
    * USB_InitComponent() if it is required.
    */

    /* Enable USBIO control on drive mode of D+ and D- pins. */
    USB_USBIO_CR1_REG &= ~ (uint32) USB_USBIO_CR1_IOMODE;

    /* Set number of LF CLK to detect UBS bus reset. */
    USB_BUS_RST_CNT_REG = USB_DEFUALT_BUS_RST_CNT;

    /* Select VBUS detection source and clear PHY isolate. The application level
    * must ensure that VBUS is valid. There is no need to wait 2us before VBUS is valid.
    */
    USB_POWER_CTRL_REG = USB_DEFAULT_POWER_CTRL_VBUS;

    /* Enable PHY detector and single-ended and differential receivers. */
    USB_POWER_CTRL_REG |= USB_DEFAULT_POWER_CTRL_PHY;

    /* Suspend clear sequence. */
    USB_POWER_CTRL_REG &= (uint32) ~USB_POWER_CTRL_SUSPEND;
    CyDelayUs(USB_WAIT_SUSPEND_DEL_DISABLE);
    USB_POWER_CTRL_REG &= (uint32) ~USB_POWER_CTRL_SUSPEND_DEL;

    /* Sets IMO lock options and clear all other bits. */
    USB_CR1_REG = USB_DEFUALT_CR1;

    /* Configure level (hi, lo, med) for each interrupt source. */
    USB_INTR_LVL_SEL_REG = USB_DEFAULT_INTR_LVL_SEL;

    /* Configure interrupt sources from: SOF, Bus Reset and EP0. */
    USB_INTR_SIE_MASK_REG = USB_DEFAULT_INTR_SIE_MASK;

#else
    uint8 enableInterrupts = CyEnterCriticalSection();

#if (USB_EP_MANAGEMENT_DMA)
    uint16 i;
#endif /* (USB_EP_MANAGEMENT_DMA) */

    /* Enable USB block. */
    USB_PM_ACT_CFG_REG |= USB_PM_ACT_EN_FSUSB;
    /* Enable USB block for Standby Power Mode. */
    USB_PM_STBY_CFG_REG |= USB_PM_STBY_EN_FSUSB;

    /* Enable core clock. */
    USB_USB_CLK_EN_REG = USB_USB_CLK_ENABLE;

    USB_CR1_REG = USB_CR1_ENABLE_LOCK;

    /* ENABLING USBIO PADS IN USB MODE FROM I/O MODE. */
    /* Ensure USB transmit enable is low (USB_USBIO_CR0.ten). - Manual Transmission - Disabled. */
    USB_USBIO_CR0_REG &= (uint8) ~USB_USBIO_CR0_TEN;
    CyDelayUs(USB_WAIT_REG_STABILITY_50NS);  /* ~50ns delay. */
    /* Disable USBIO by asserting PM.USB_CR0.fsusbio_pd_n(Inverted.
    *  high. These bits will be set low by the power manager out-of-reset.
    *  Also confirm USBIO pull-up is disabled.
    */
    USB_PM_USB_CR0_REG &= (uint8) ~(USB_PM_USB_CR0_PD_N |
                                                 USB_PM_USB_CR0_PD_PULLUP_N);

    /* Select IOMODE to USB mode. */
    USB_USBIO_CR1_REG &= (uint8) ~USB_USBIO_CR1_IOMODE;

    /* Enable USBIO reference by setting PM.USB_CR0.fsusbio_ref_en. */
    USB_PM_USB_CR0_REG |= USB_PM_USB_CR0_REF_EN;
    /* Reference is available for 1us after regulator is enabled. */
    CyDelayUs(USB_WAIT_REG_STABILITY_1US);
    /* OR 40us after power is restored. */
    CyDelayUs(USB_WAIT_VREF_RESTORE);
    /* Ensure single-ended disable bits are low (PRT15.INP_DIS[7:6])(input receiver enabled). */
    USB_DM_INP_DIS_REG &= (uint8) ~USB_DM_MASK;
    USB_DP_INP_DIS_REG &= (uint8) ~USB_DP_MASK;

    /* Enable USBIO. */
    USB_PM_USB_CR0_REG |= USB_PM_USB_CR0_PD_N;
    CyDelayUs(USB_WAIT_PD_PULLUP_N_ENABLE);
    /* Set USBIO pull-up enable. */
    USB_PM_USB_CR0_REG |= USB_PM_USB_CR0_PD_PULLUP_N;

    /* Reset Arbiter Write Address register for endpoint 1. */
    CY_SET_REG8(USB_ARB_RW1_WA_PTR,     0u);
    CY_SET_REG8(USB_ARB_RW1_WA_MSB_PTR, 0u);

#if (USB_EP_MANAGEMENT_DMA)
    /* Initialize transfer descriptor. This will be used to detect DMA state - initialized or not. */
    for (i = 0u; i < USB_MAX_EP; ++i)
    {
        USB_DmaTd[i] = DMA_INVALID_TD;

    #if (USB_EP_MANAGEMENT_DMA_AUTO && (USB_EP_DMA_AUTO_OPT == 0u))
        USB_DmaNextTd[i] = DMA_INVALID_TD;
    #endif /* (USB_EP_MANAGEMENT_DMA_AUTO && (USB_EP_DMA_AUTO_OPT == 0u)) */
    }
#endif /* (USB_EP_MANAGEMENT_DMA) */

    CyExitCriticalSection(enableInterrupts);
#endif /* (CY_PSOC4) */

    /* Configure interrupts from USB block. */
#if (CY_PSOC4)
    /* Configure hi_int: set handler and priority. */
    CyIntSetPriority     (USB_INTR_HI_VECT_NUM,  USB_INTR_HI_PRIORITY);
    (void) CyIntSetVector(USB_INTR_HI_VECT_NUM, &USB_INTR_HI_ISR);

    /* Configure lo_int: set handler and priority. */
    CyIntSetPriority     (USB_INTR_LO_VECT_NUM,  USB_INTR_LO_PRIORITY);
    (void) CyIntSetVector(USB_INTR_LO_VECT_NUM, &USB_INTR_LO_ISR);

    /* Configure med_int: set handler and priority (routed through DSI). */
    CyIntSetPriority     (USB_INTR_MED_VECT_NUM,  USB_INTR_MED_PRIORITY);
    (void) CyIntSetVector(USB_INTR_MED_VECT_NUM, &USB_INTR_MED_ISR);

#else
    /* Set bus reset interrupt. */
    CyIntSetPriority(USB_BUS_RESET_VECT_NUM, USB_BUS_RESET_PRIOR);
    (void) CyIntSetVector(USB_BUS_RESET_VECT_NUM,   &USB_BUS_RESET_ISR);

    /* Set Control Endpoint Interrupt. */
    CyIntSetPriority(USB_EP_0_VECT_NUM, USB_EP_0_PRIOR);
    (void) CyIntSetVector(USB_EP_0_VECT_NUM,   &USB_EP_0_ISR);

    /* Set SOF interrupt. */
    #if (USB_SOF_ISR_ACTIVE)
        CyIntSetPriority     (USB_SOF_VECT_NUM,  USB_SOF_PRIOR);
        (void) CyIntSetVector(USB_SOF_VECT_NUM, &USB_SOF_ISR);
    #endif /* (USB_SOF_ISR_ACTIVE) */

    /* Set Data Endpoint 1 Interrupt. */
    #if (USB_EP1_ISR_ACTIVE)
        CyIntSetPriority     (USB_EP_1_VECT_NUM,  USB_EP_1_PRIOR);
        (void) CyIntSetVector(USB_EP_1_VECT_NUM,  &USB_EP_1_ISR);
    #endif /* (USB_EP1_ISR_ACTIVE) */

    /* Set Data Endpoint 2 Interrupt. */
    #if (USB_EP2_ISR_ACTIVE)
        CyIntSetPriority     (USB_EP_2_VECT_NUM,  USB_EP_2_PRIOR);
        (void) CyIntSetVector(USB_EP_2_VECT_NUM, &USB_EP_2_ISR);
    #endif /* (USB_EP2_ISR_ACTIVE) */

    /* Set Data Endpoint 3 Interrupt. */
    #if (USB_EP3_ISR_ACTIVE)
        CyIntSetPriority     (USB_EP_3_VECT_NUM,  USB_EP_3_PRIOR);
        (void) CyIntSetVector(USB_EP_3_VECT_NUM, &USB_EP_3_ISR);
    #endif /* (USB_EP3_ISR_ACTIVE) */

    /* Set Data Endpoint 4 Interrupt. */
    #if (USB_EP4_ISR_ACTIVE)
        CyIntSetPriority     (USB_EP_4_VECT_NUM,  USB_EP_4_PRIOR);
        (void) CyIntSetVector(USB_EP_4_VECT_NUM, &USB_EP_4_ISR);
    #endif /* (USB_EP4_ISR_ACTIVE) */

    /* Set Data Endpoint 5 Interrupt. */
    #if (USB_EP5_ISR_ACTIVE)
        CyIntSetPriority     (USB_EP_5_VECT_NUM,  USB_EP_5_PRIOR);
        (void) CyIntSetVector(USB_EP_5_VECT_NUM, &USB_EP_5_ISR);
    #endif /* (USB_EP5_ISR_ACTIVE) */

    /* Set Data Endpoint 6 Interrupt. */
    #if (USB_EP6_ISR_ACTIVE)
        CyIntSetPriority     (USB_EP_6_VECT_NUM,  USB_EP_6_PRIOR);
        (void) CyIntSetVector(USB_EP_6_VECT_NUM, &USB_EP_6_ISR);
    #endif /* (USB_EP6_ISR_ACTIVE) */

     /* Set Data Endpoint 7 Interrupt. */
    #if (USB_EP7_ISR_ACTIVE)
        CyIntSetPriority     (USB_EP_7_VECT_NUM,  USB_EP_7_PRIOR);
        (void) CyIntSetVector(USB_EP_7_VECT_NUM, &USB_EP_7_ISR);
    #endif /* (USB_EP7_ISR_ACTIVE) */

    /* Set Data Endpoint 8 Interrupt. */
    #if (USB_EP8_ISR_ACTIVE)
        CyIntSetPriority     (USB_EP_8_VECT_NUM,  USB_EP_8_PRIOR);
        (void) CyIntSetVector(USB_EP_8_VECT_NUM, &USB_EP_8_ISR);
    #endif /* (USB_EP8_ISR_ACTIVE) */

    /* Set ARB Interrupt. */
    #if (USB_EP_MANAGEMENT_DMA && USB_ARB_ISR_ACTIVE)
        CyIntSetPriority     (USB_ARB_VECT_NUM,  USB_ARB_PRIOR);
        (void) CyIntSetVector(USB_ARB_VECT_NUM, &USB_ARB_ISR);
    #endif /* (USB_EP_MANAGEMENT_DMA && USB_ARB_ISR_ACTIVE) */
#endif /* (CY_PSOC4) */

    /* Common: Configure GPIO interrupt for wakeup. */
#if (USB_DP_ISR_ACTIVE)
    CyIntSetPriority     (USB_DP_INTC_VECT_NUM,  USB_DP_INTC_PRIORITY);
    (void) CyIntSetVector(USB_DP_INTC_VECT_NUM, &USB_DP_ISR);
#endif /* (USB_DP_ISR_ACTIVE) */

#if (USB_EP_MANAGEMENT_DMA && CY_PSOC4)
    /* Initialize DMA channels. */
    USB_InitEpDma();
#endif /* (USB_EP_MANAGEMENT_DMA && CY_PSOC4) */
}
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
