spiricom/Electrobass_embedded/PSOC5_electrobass_stringsensors_fornextRev_largerpart/CE210514_PSOC3_5_Thermistor.cydsn/codegentemp/USB.h

/***************************************************************************//**
* \file  USB.h
* \version 3.20
*
* \brief
*  This file provides function prototypes and constants for the USBFS component. 
*
********************************************************************************
* \copyright
* Copyright 2008-2016, Cypress Semiconductor Corporation.  All rights reserved.
* You may use this file only in accordance with the license, terms, conditions,
* disclaimers, and limitations in the end user license agreement accompanying
* the software package with which this file was provided.
*******************************************************************************/

#if !defined(CY_USBFS_USB_H)
#define CY_USBFS_USB_H

#include "cydevice_trm.h"
#include "cyfitter.h"
#include "cytypes.h"
#include "CyLib.h"


/*  User supplied definitions. */
/* `#START USER_DEFINITIONS` Place your declaration here */

/* `#END` */

/***************************************
* Enumerated Types and Parameters
***************************************/

/* USB IP memory management options. */
#define USB__EP_MANUAL    (0u)
#define USB__EP_DMAMANUAL (1u)
#define USB__EP_DMAAUTO   (2u)

/* USB IP memory allocation options. */
#define USB__MA_STATIC    (0u)
#define USB__MA_DYNAMIC   (1u)


/***************************************
*    Initial Parameter Constants
***************************************/

#define USB_NUM_DEVICES                        (1u)
#define USB_ENABLE_AUDIO_CLASS                 
#define USB_ENABLE_MIDI_CLASS                  (1u)
#define USB_ENABLE_MSC_CLASS                   (0u)
#define USB_BOS_ENABLE                         (0u)
#define USB_ENABLE_DESCRIPTOR_STRINGS          
#define USB_ENABLE_SN_STRING                   
#define USB_ENABLE_IDSN_STRING                 
#define USB_ENABLE_STRINGS                     
#define USB_MAX_REPORTID_NUMBER                (0u)

#define USB_MON_VBUS               (1u)
#define USB_EXTERN_VBUS            (1u)
#define USB_POWER_PAD_VBUS         (0u)
#define USB_EXTERN_VND             (0u)
#define USB_EXTERN_CLS             (0u)
#define USB_MAX_INTERFACES_NUMBER  (2u)
#define USB_EP_MM                  (2u)
#define USB_EP_MA                  (0u)
#define USB_ENABLE_BATT_CHARG_DET  (0u)
#define USB_GEN_16BITS_EP_ACCESS   (1u)

/* Enable Class APIs: MIDI, CDC, MSC. */         
#define USB_ENABLE_CDC_CLASS_API   (0u != (1u))
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
